Joanna610/Quadrature-amplitude-modulator/antennas_graphs/directional_pattern.jpg

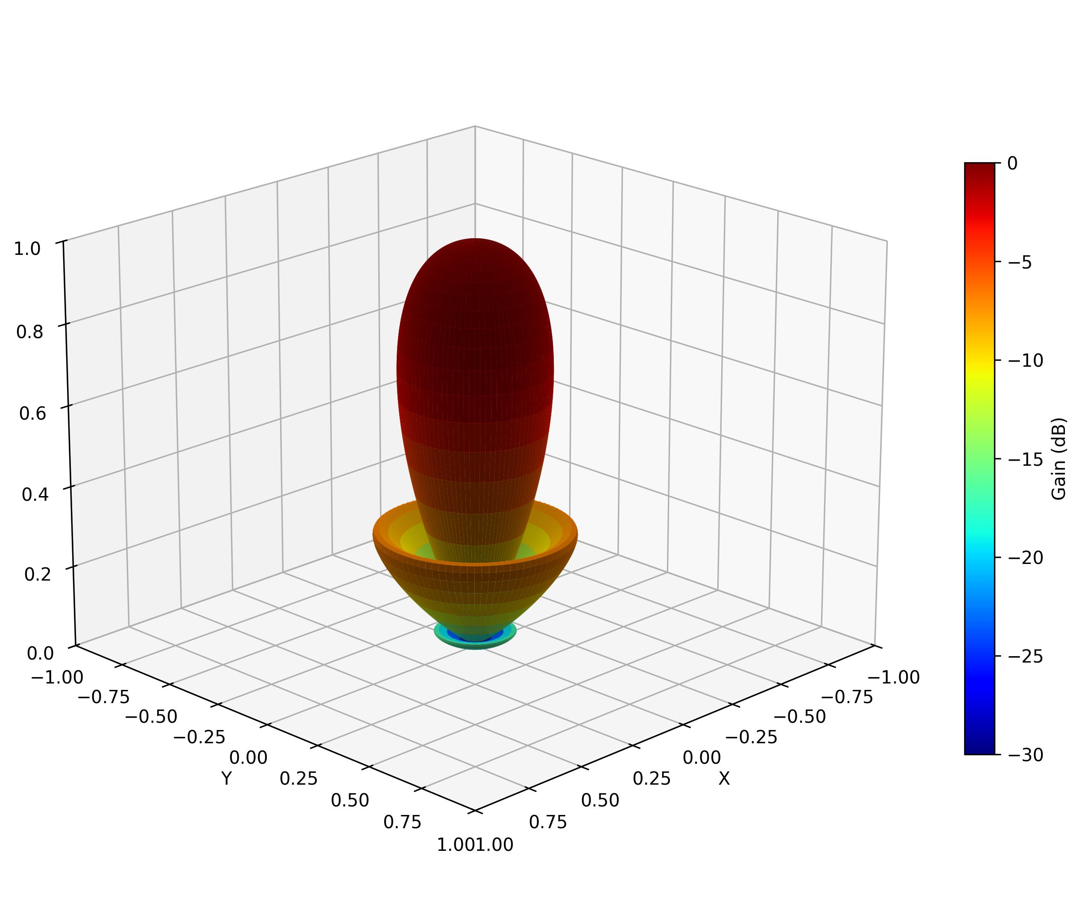
antennas_graphs/directional_pattern.jpg
