Joanna610/Quadrature-amplitude-modulator/antennas_graphs/omi_radiation pattern.jpg

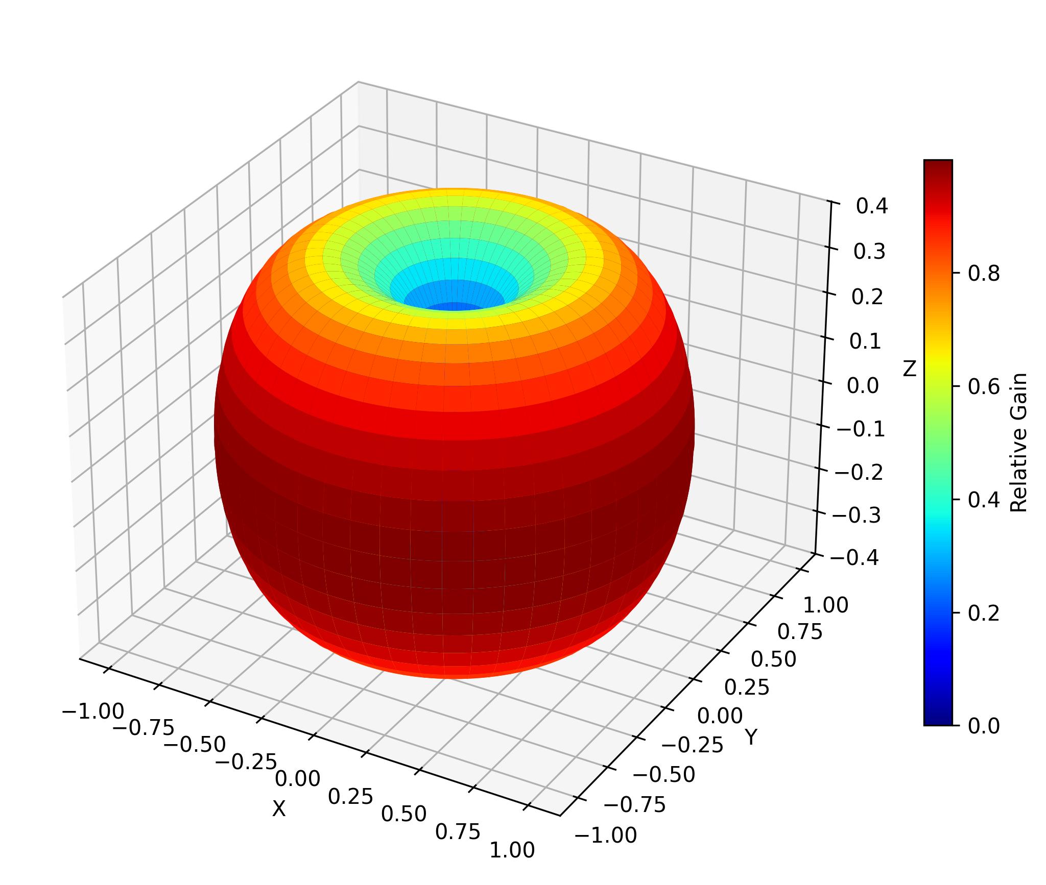
antennas_graphs/omi_radiation pattern.jpg
