Joanna610/Quadrature-amplitude-modulator/antennas_graphs/omi_vertycal.jpg

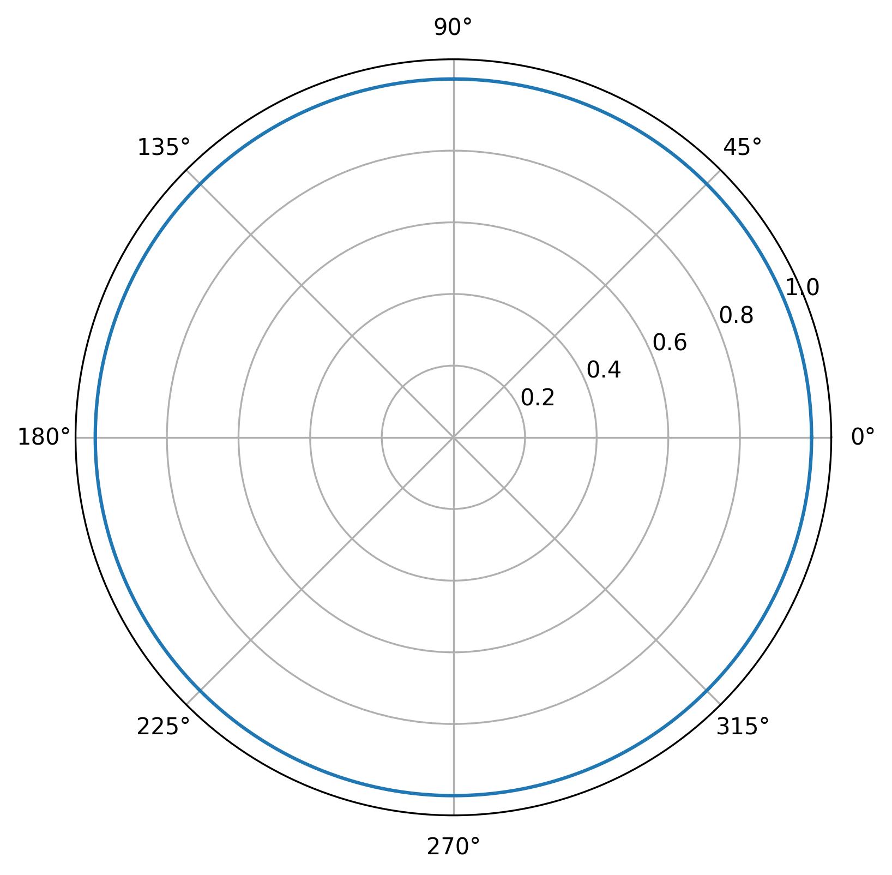
antennas_graphs/omi_vertycal.jpg
