Joanna610/Quadrature-amplitude-modulator/antennas_graphs/omni_2d.jpg

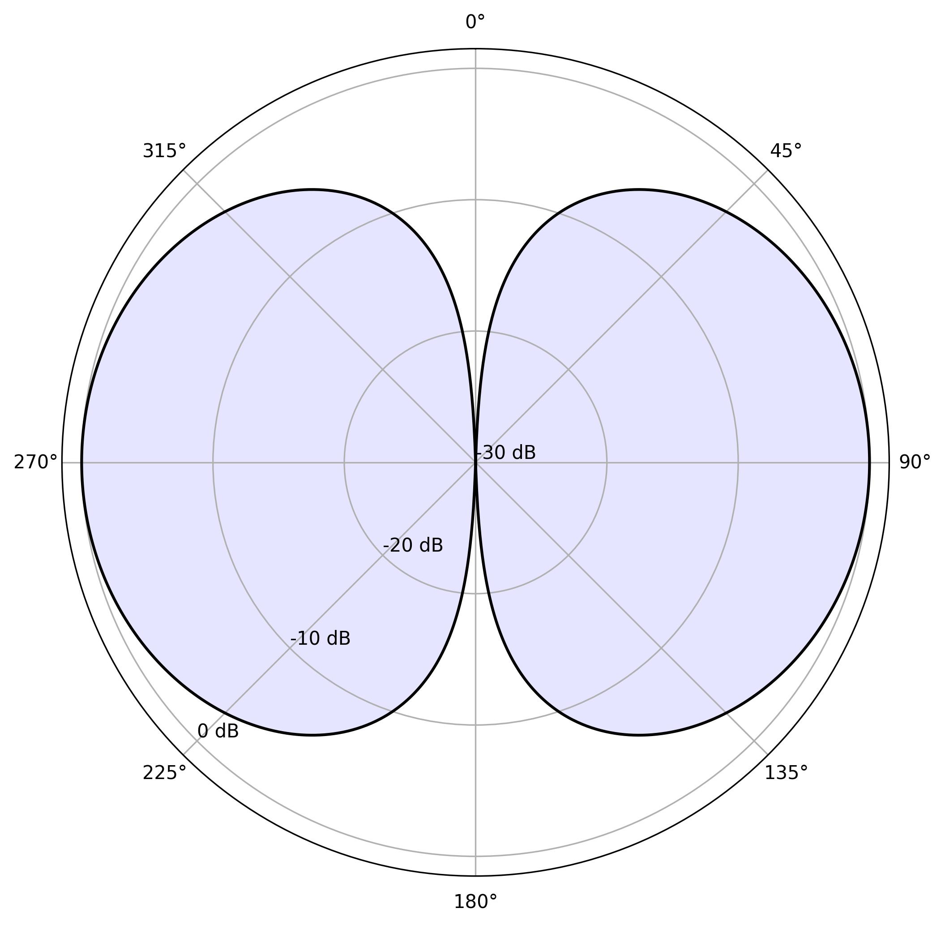
antennas_graphs/omni_2d.jpg
