Joanna610/Quadrature-amplitude-modulator/antennas_graphs/omni_3d.jpg

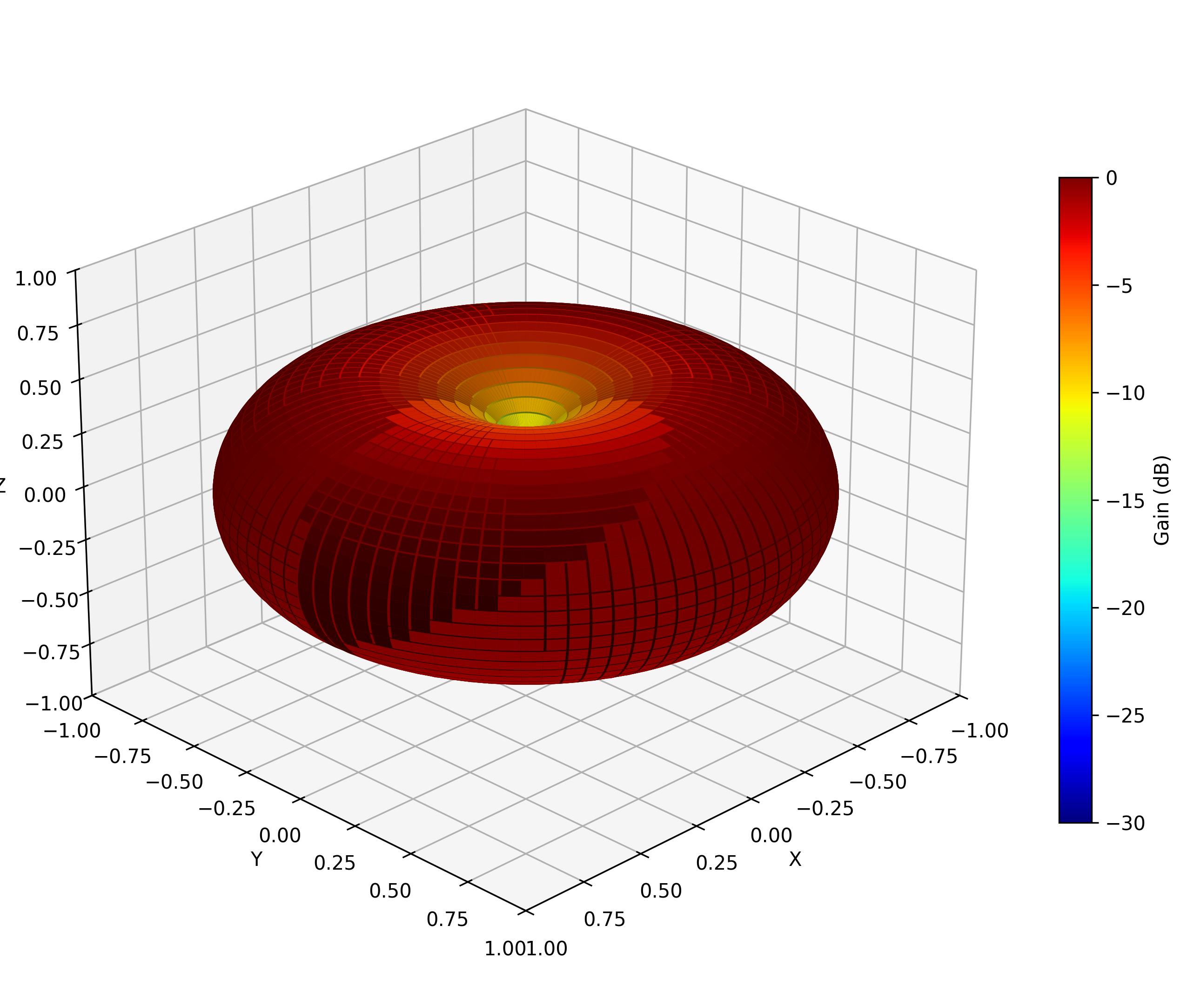
antennas_graphs/omni_3d.jpg
