Joanna610/Quadrature-amplitude-modulator/modulation_graph/4_QAM.jpg

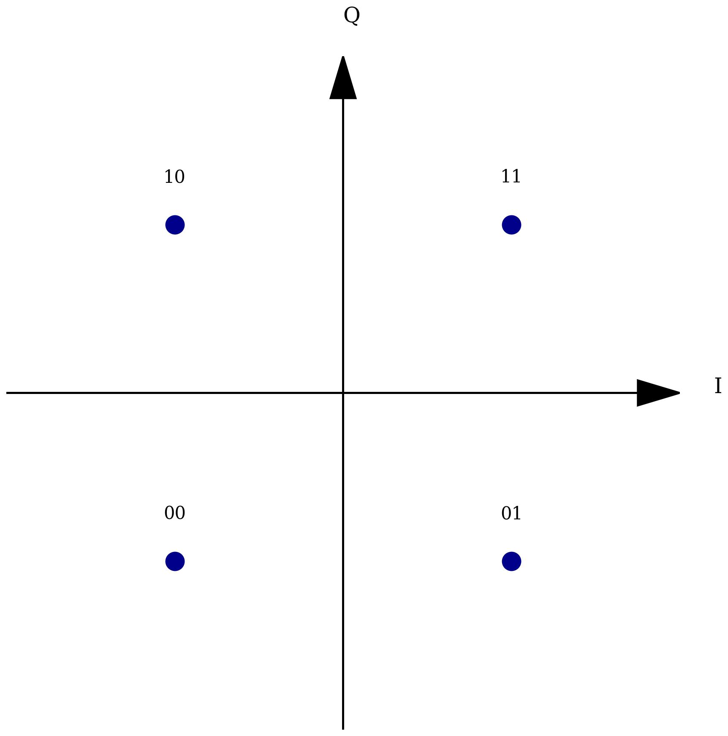
modulation_graph/4_QAM.jpg
