Joanna610/Quadrature-amplitude-modulator/modulation_graph/8PSK.jpg

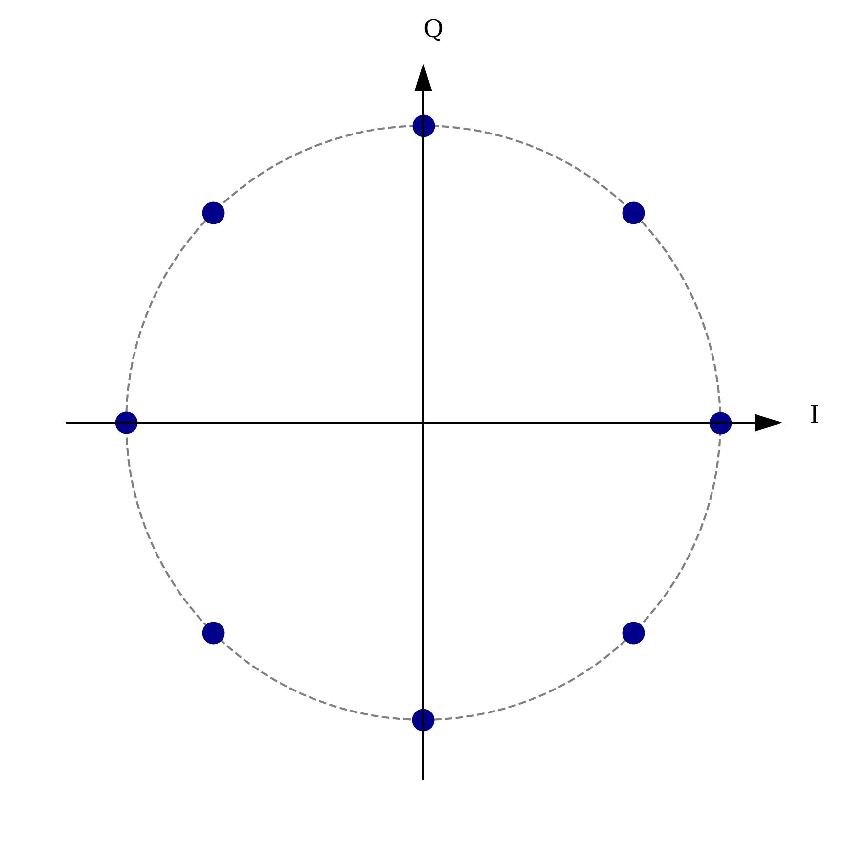
modulation_graph/8PSK.jpg
