Joanna610/Quadrature-amplitude-modulator/modulation_graph/16_QAM.jpg

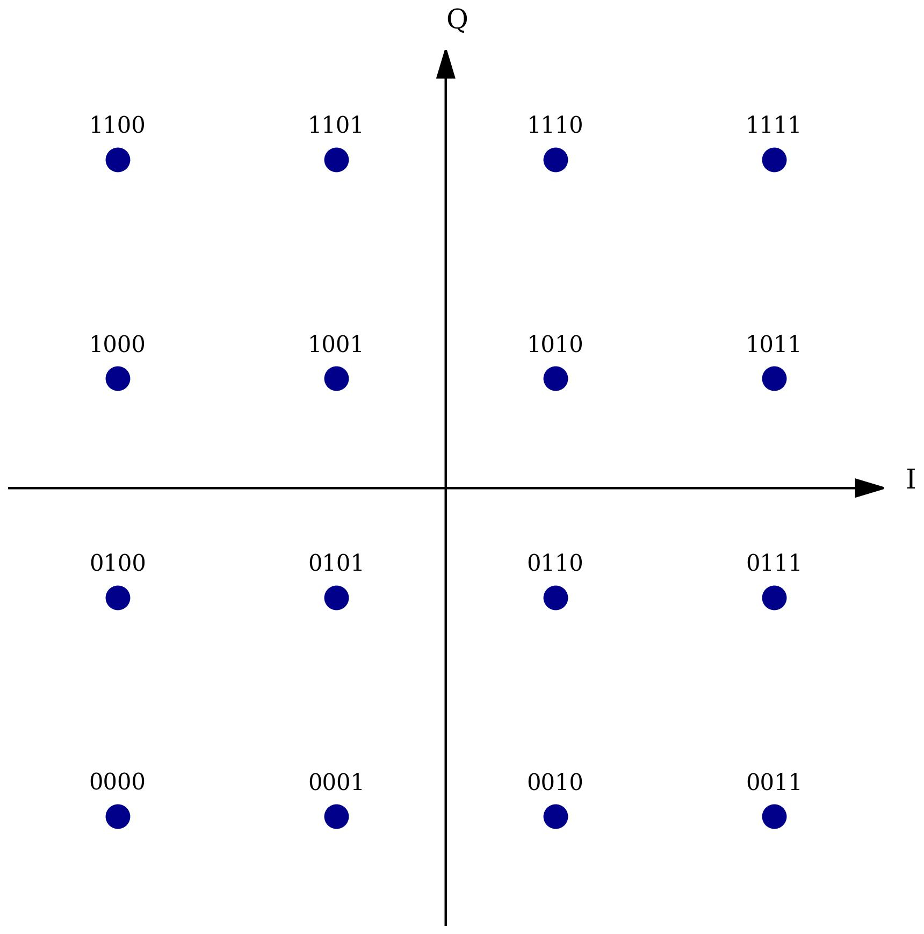
modulation_graph/16_QAM.jpg
