Joanna610/Quadrature-amplitude-modulator/modulation_graph/amplitude_carrier.png

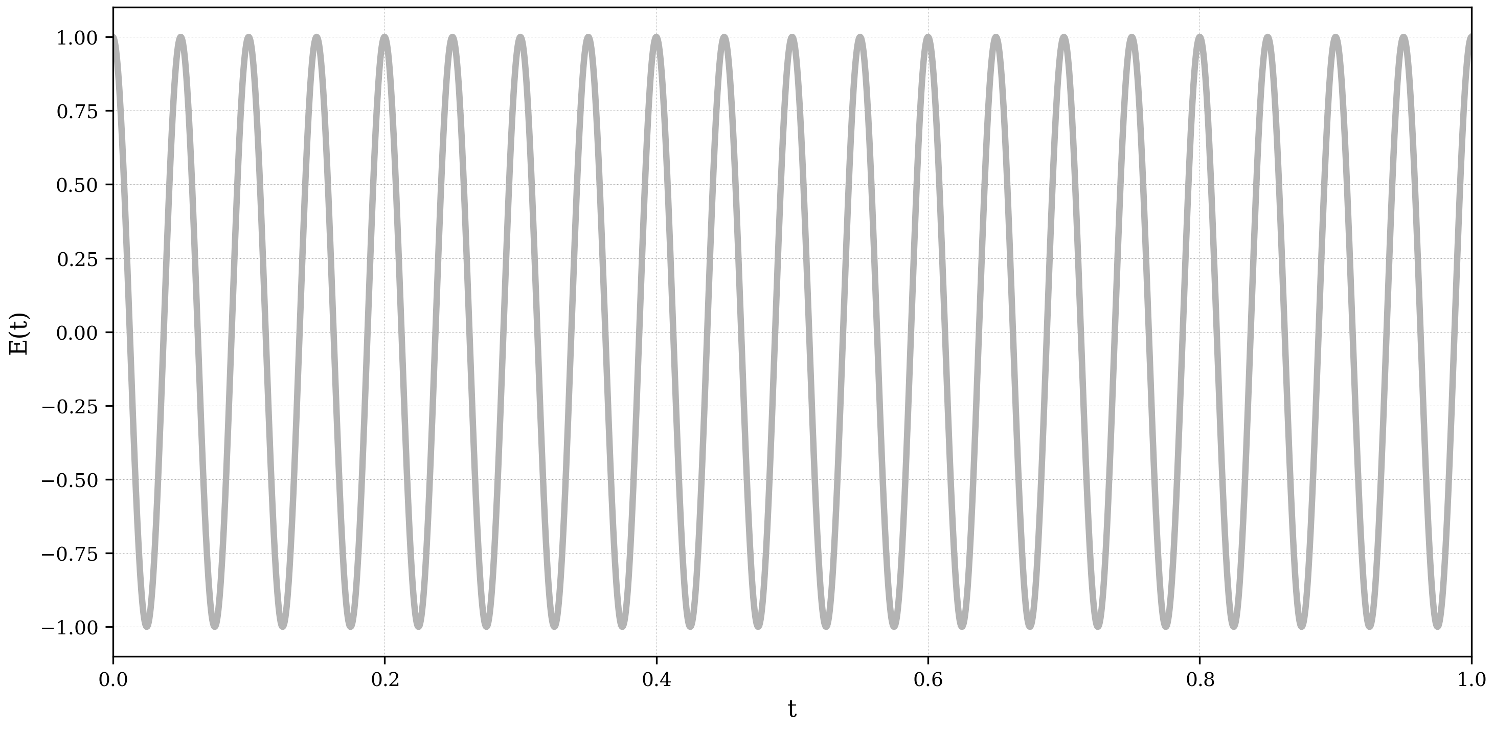
modulation_graph/amplitude_carrier.png
