Joanna610/Quadrature-amplitude-modulator/modulation_graph/amplitude_modulation.jpg

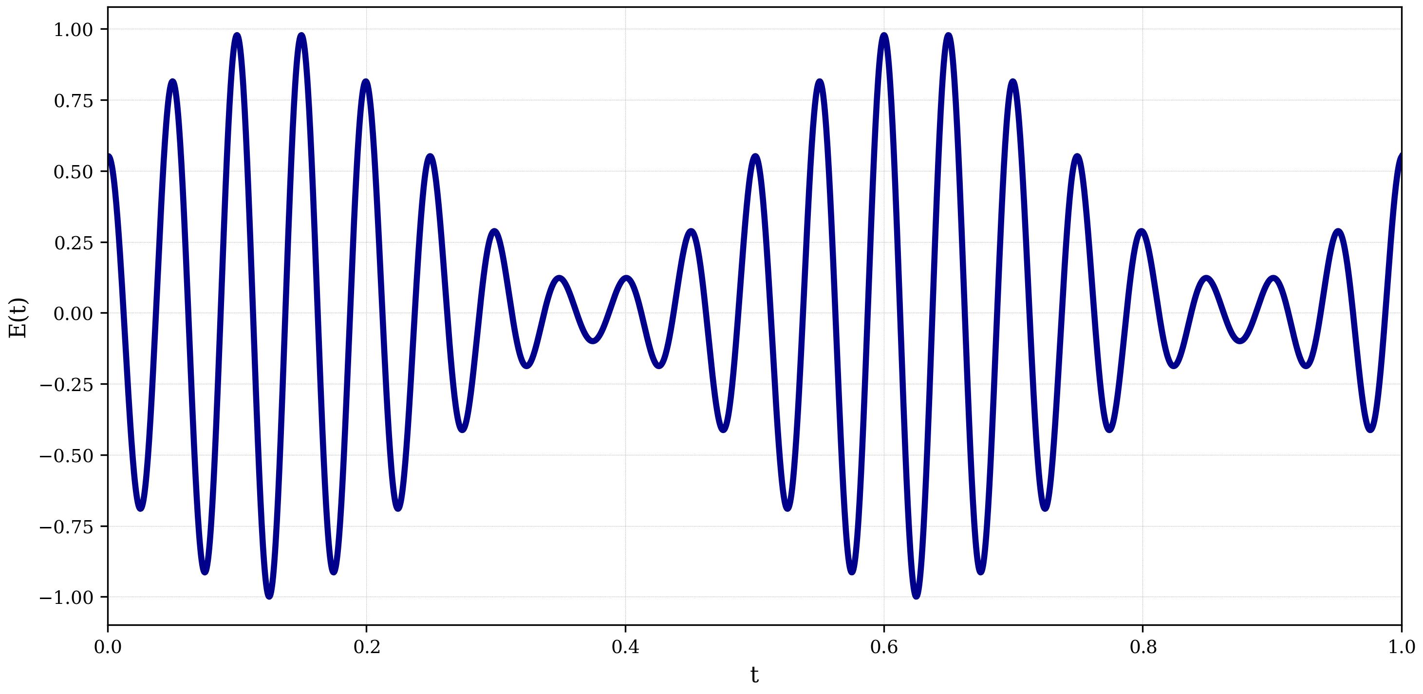
modulation_graph/amplitude_modulation.jpg
