Joanna610/Quadrature-amplitude-modulator/modulation_graph/amplitude_signal.png

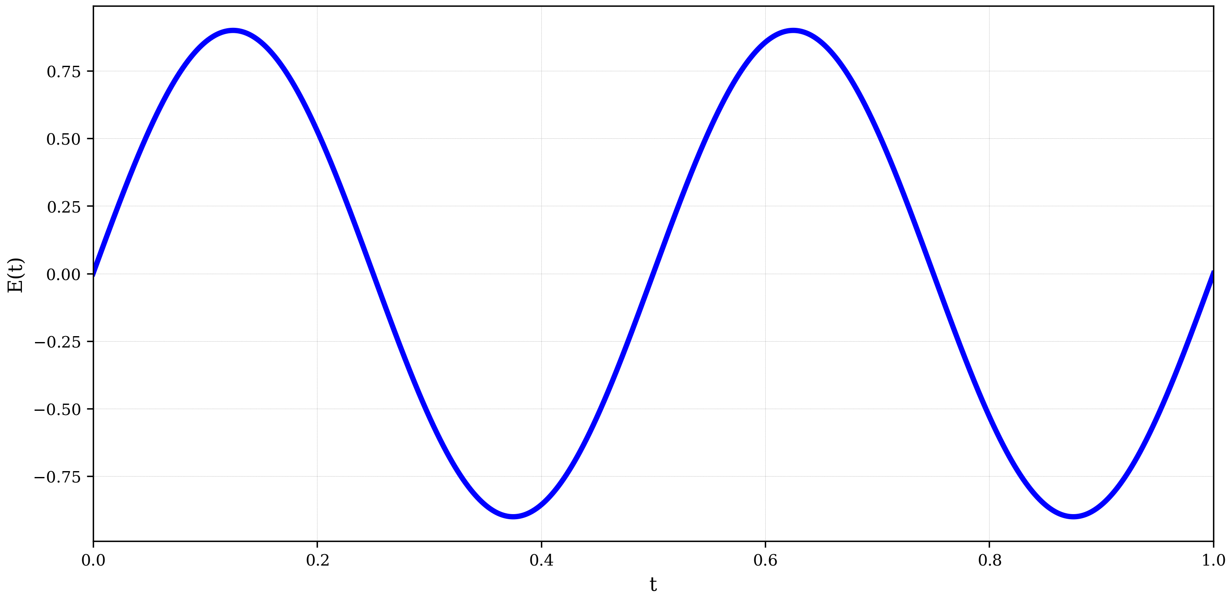
modulation_graph/amplitude_signal.png
