Joanna610/Quadrature-amplitude-modulator/modulation_graph/ASK.jpg

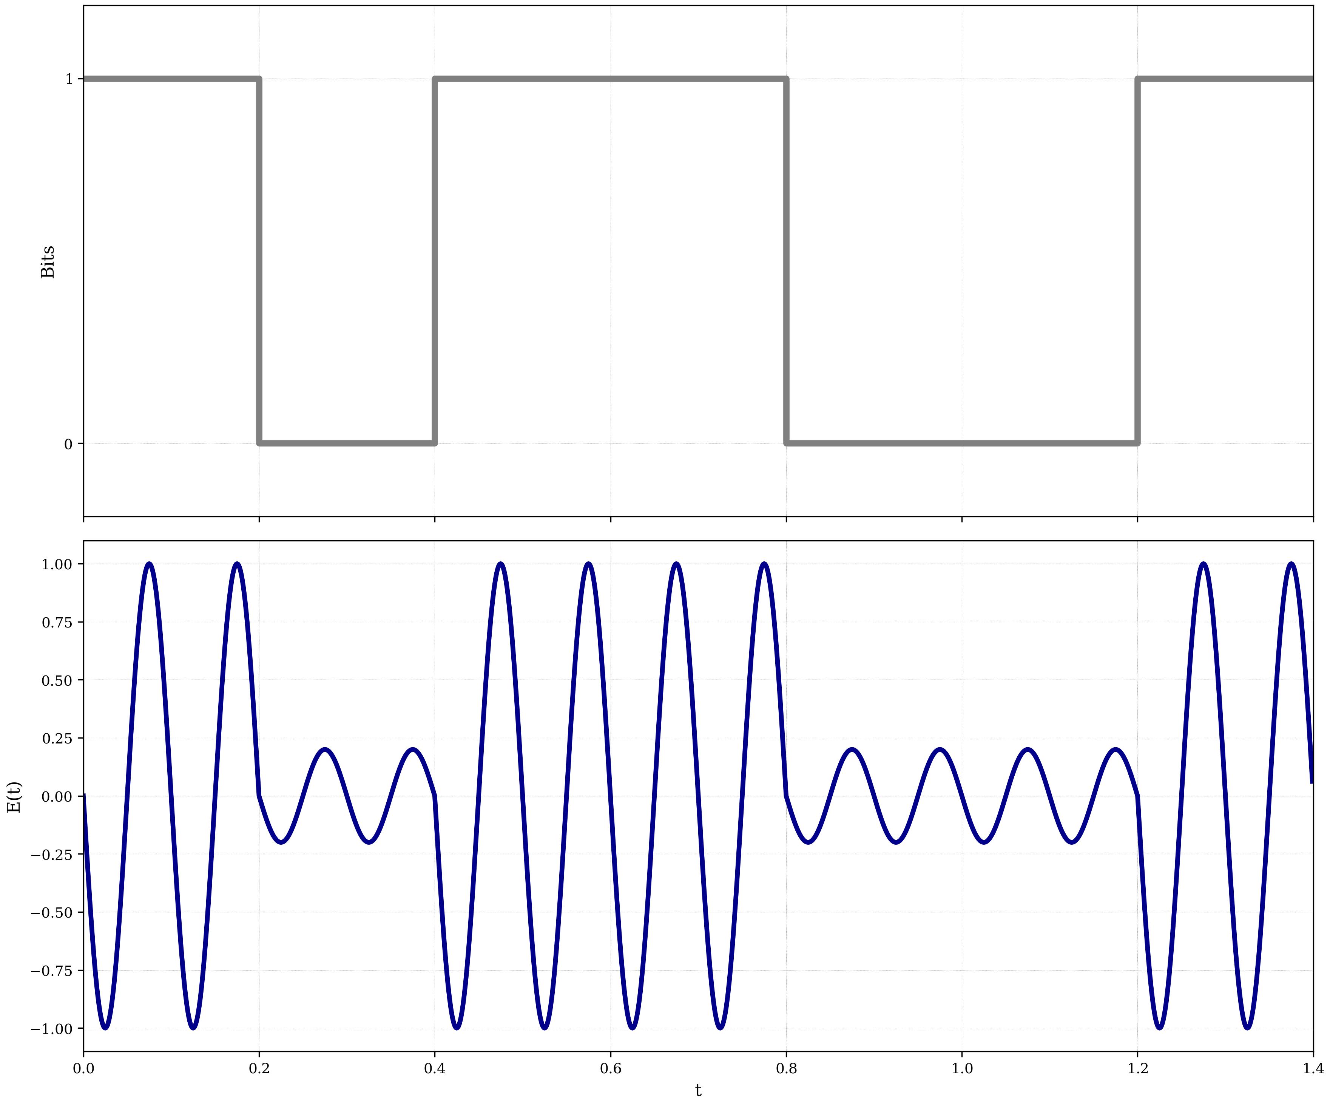
modulation_graph/ASK.jpg
