Joanna610/Quadrature-amplitude-modulator/modulation_graph/bpsk.jpg

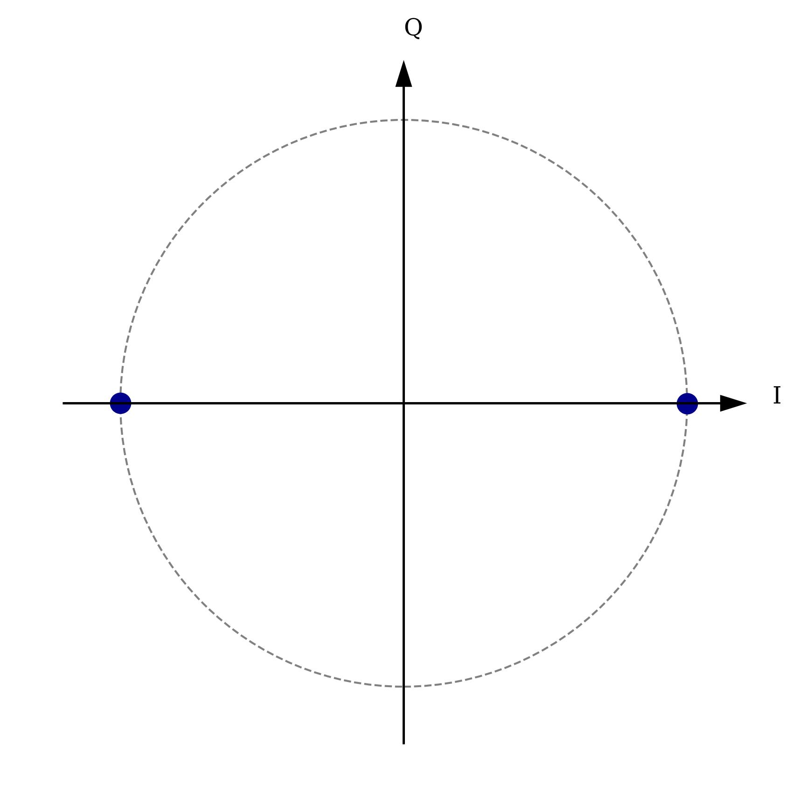
modulation_graph/bpsk.jpg
