Joanna610/Quadrature-amplitude-modulator/modulation_graph/frequency_modulation.jpg

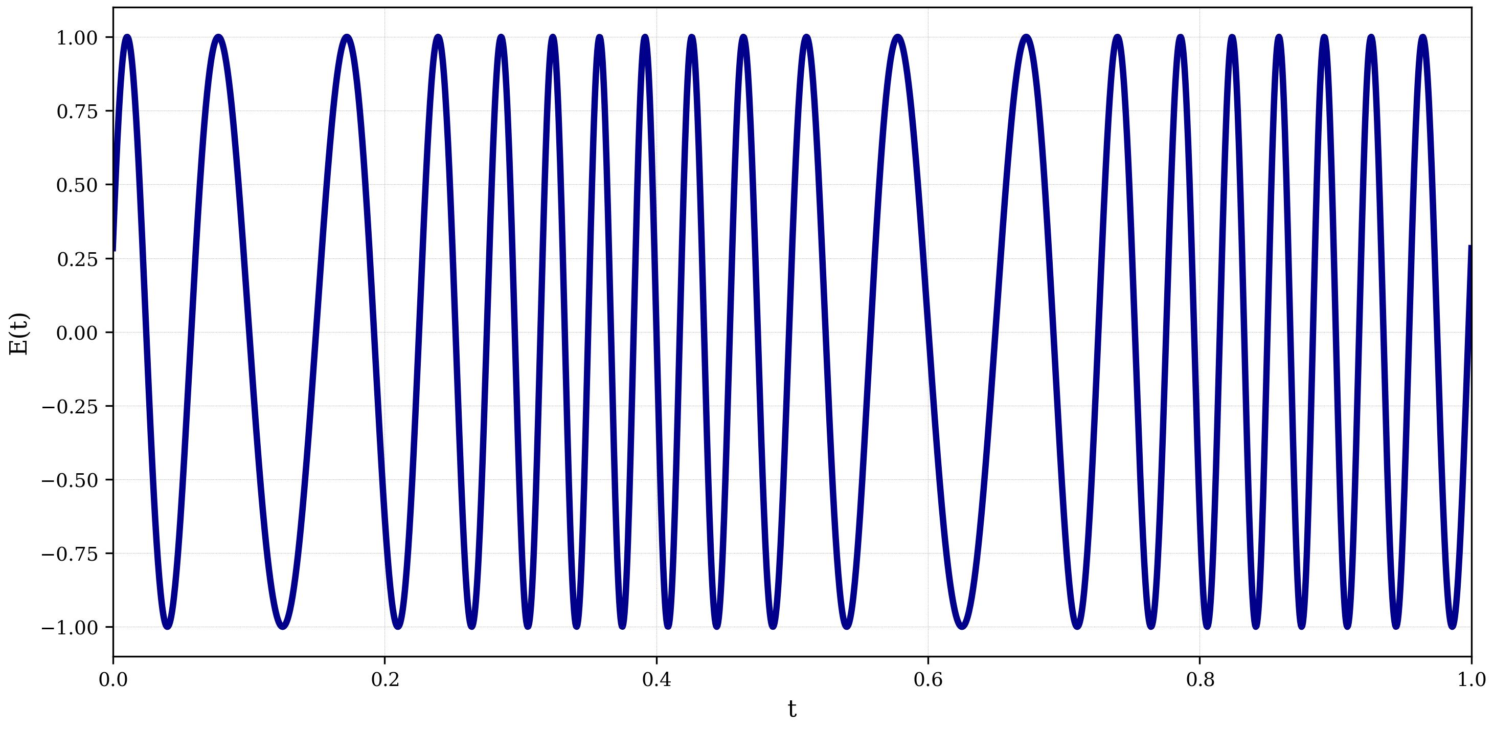
modulation_graph/frequency_modulation.jpg
