Joanna610/Quadrature-amplitude-modulator/modulation_graph/frequency_signal.png

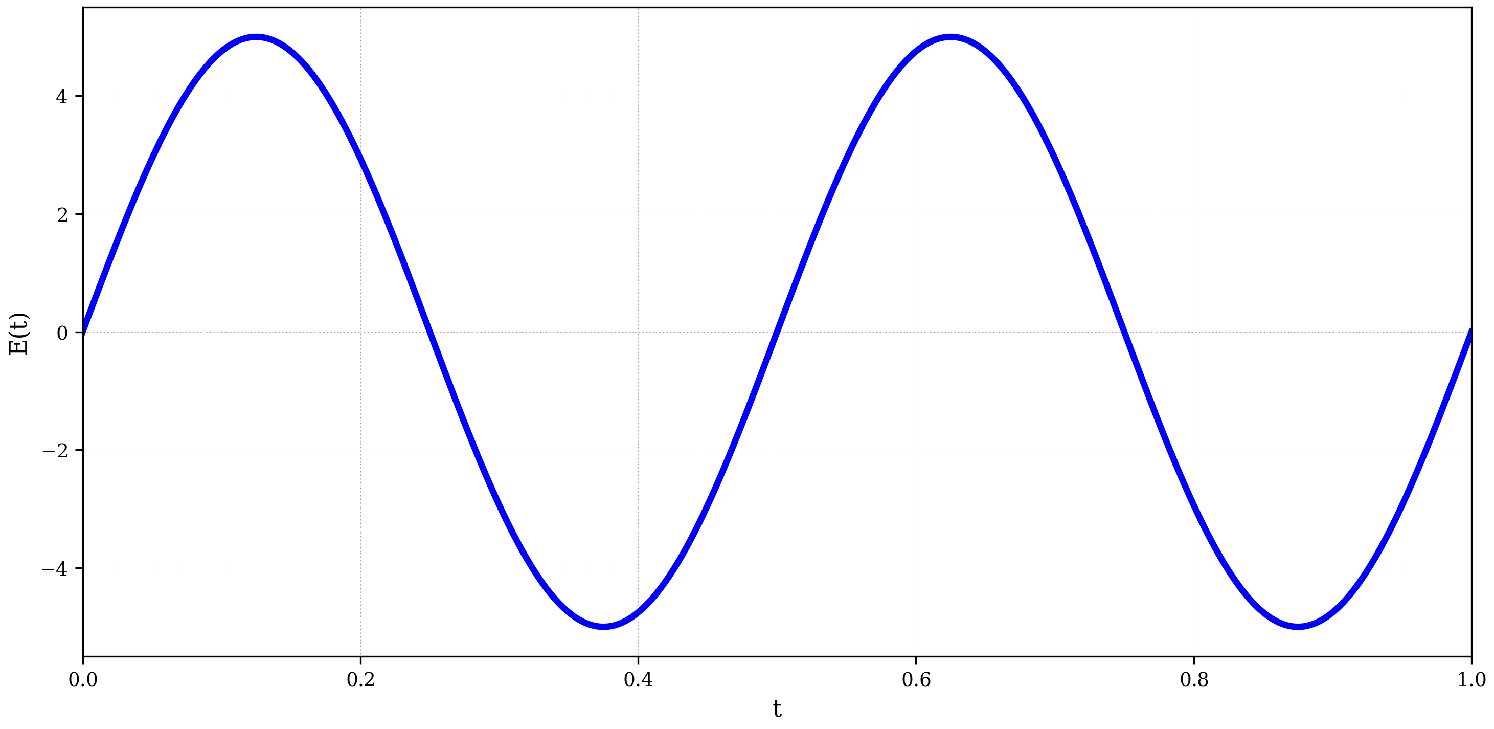
modulation_graph/frequency_signal.png
