Joanna610/Quadrature-amplitude-modulator/modulation_graph/FSK.jpg

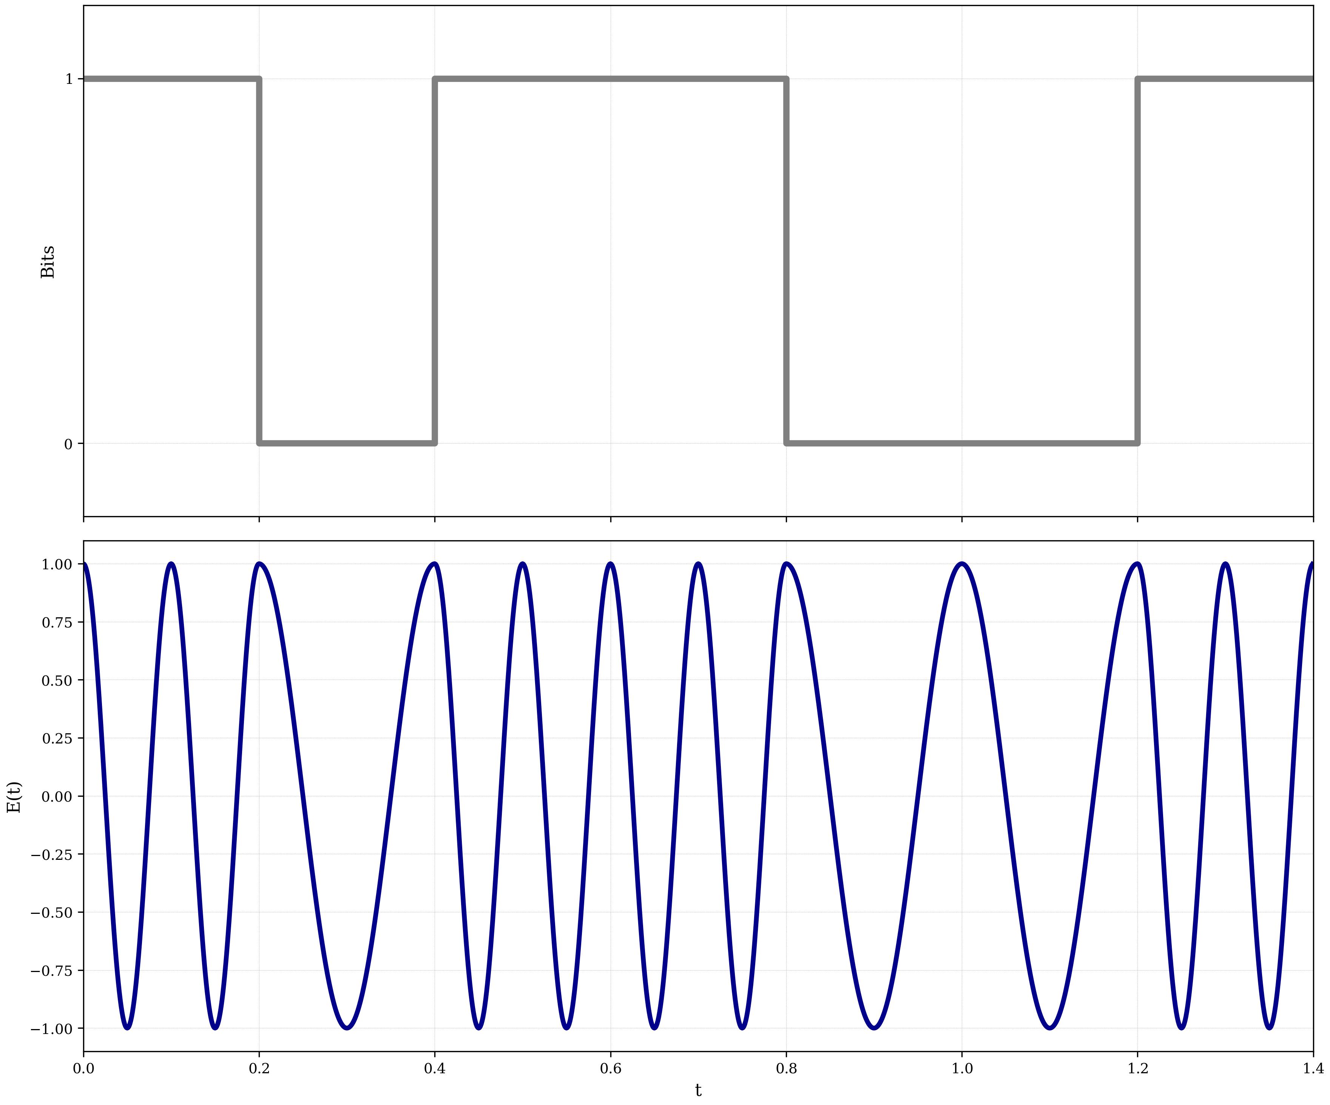
modulation_graph/FSK.jpg
