Joanna610/Quadrature-amplitude-modulator/modulation_graph/phase_modulation.jpg

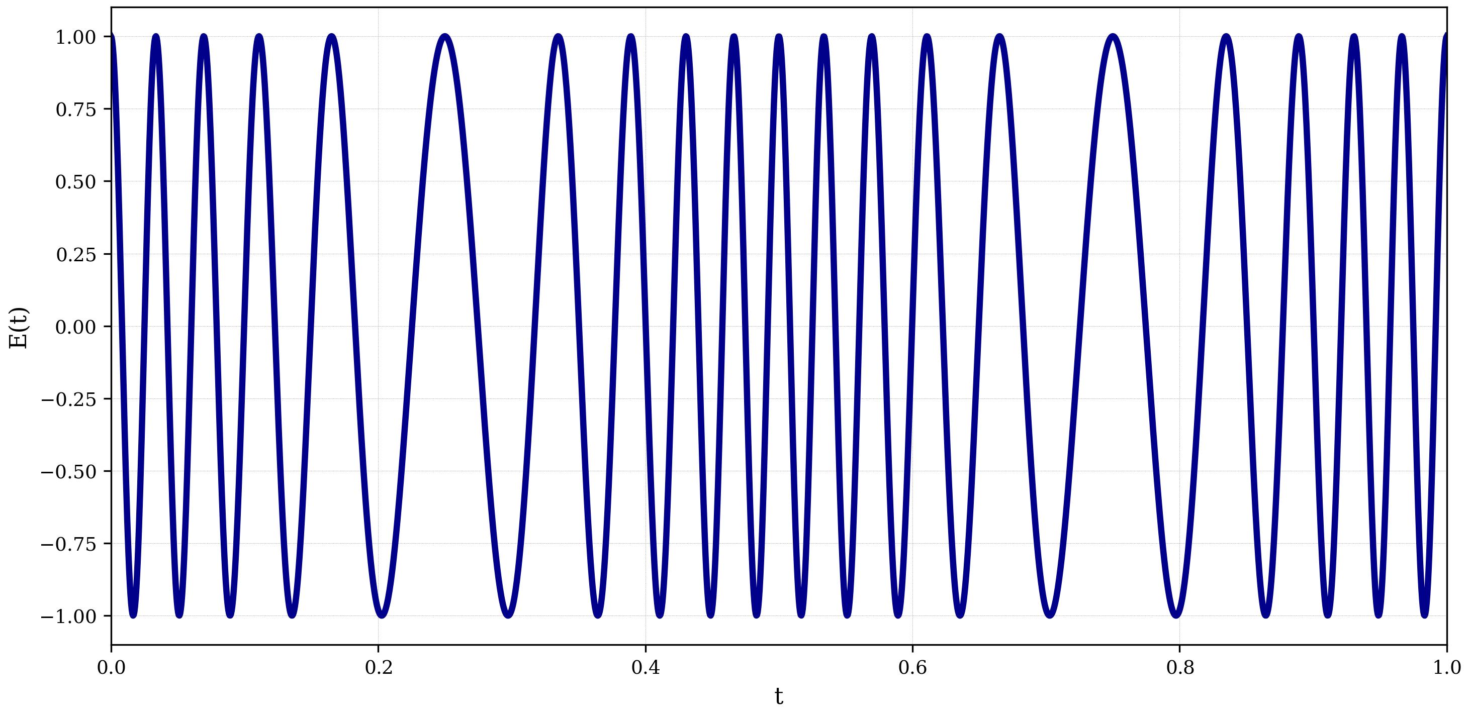
modulation_graph/phase_modulation.jpg
