Joanna610/Quadrature-amplitude-modulator/modulation_graph/PSK.jpg

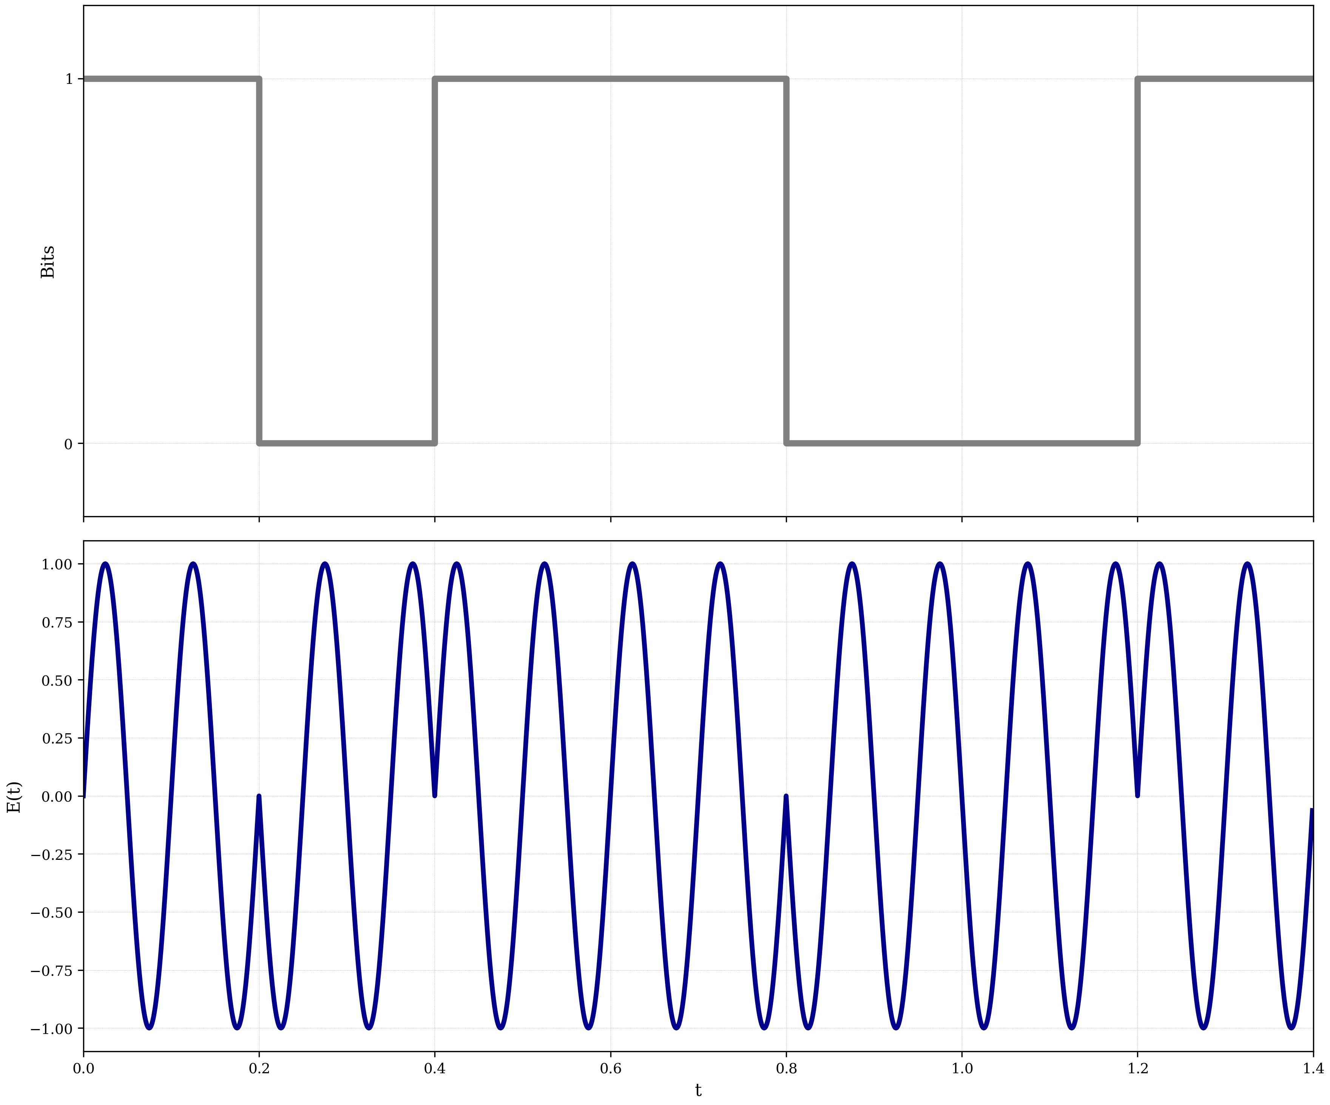
modulation_graph/PSK.jpg
