Joanna610/Quadrature-amplitude-modulator/transmiter/max2608.png

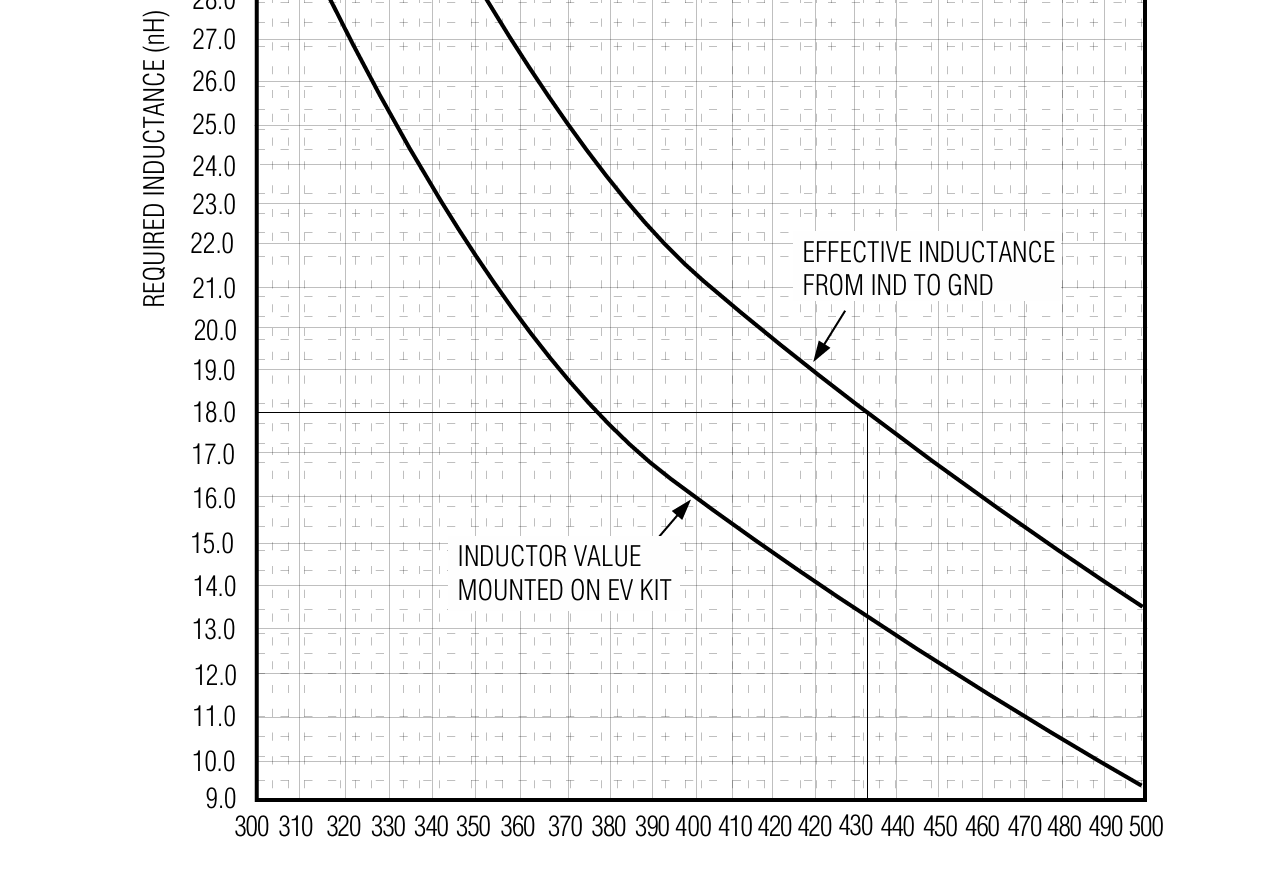
transmiter/max2608.png
