Joanna610/Quadrature-amplitude-modulator/wave.png

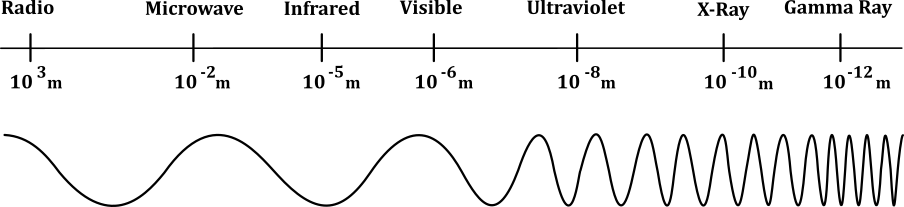
wave.png
