Joanna610/Quadrature-amplitude-modulator/antennas_graphs/test.jpg

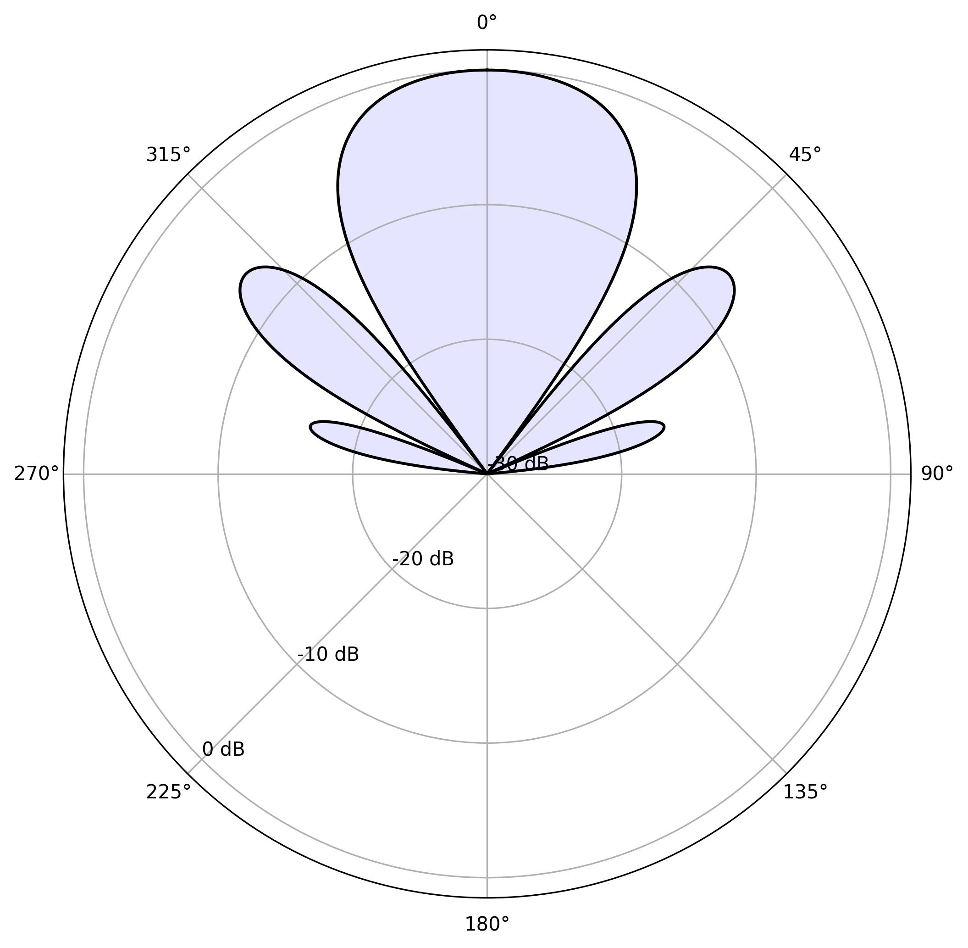
antennas_graphs/test.jpg
