Joanna610/Quadrature-amplitude-modulator/receiver/measurements/all_system_different_frequencies/gen_413_output_-16dBm.png

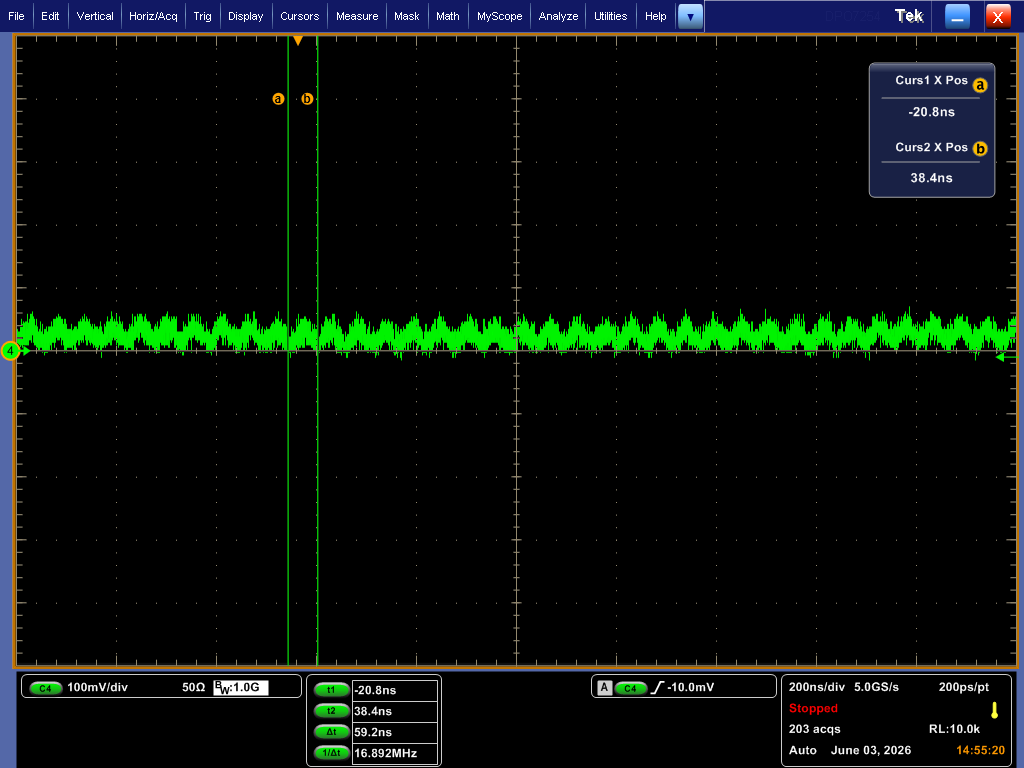
receiver/measurements/all_system_different_frequencies/gen_413_output_-16dBm.png
