Joanna610/Quadrature-amplitude-modulator/receiver/measurements/all_system_together_433MHz/433MHz_-13dBm_RF_from_transformator.png

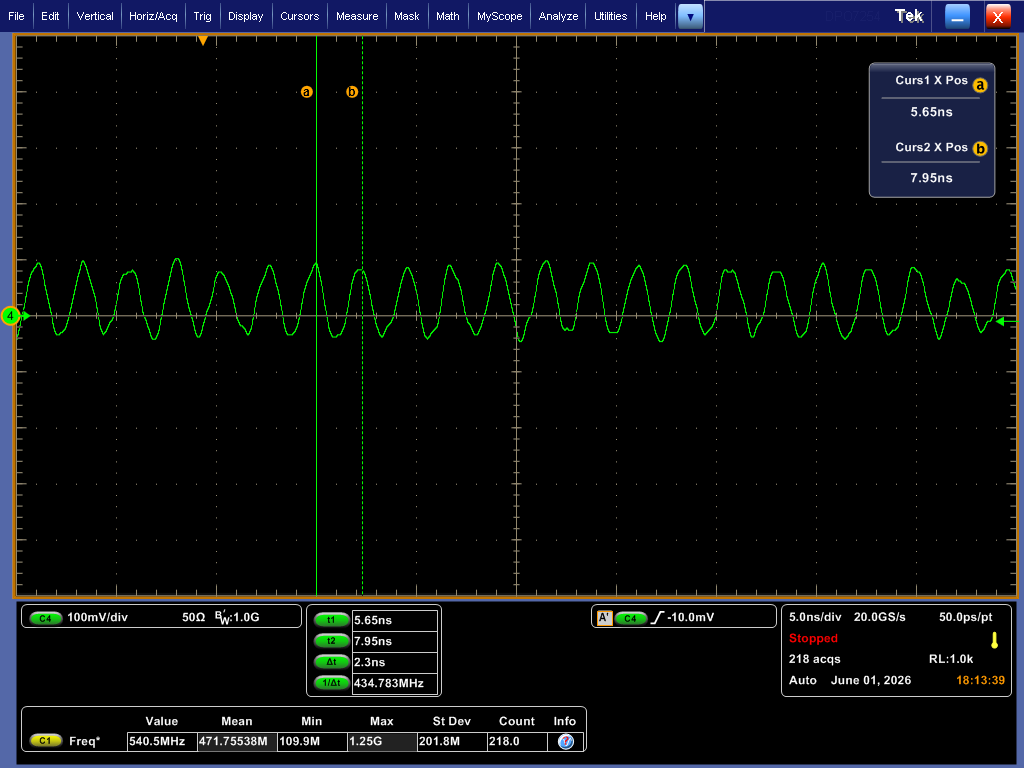
receiver/measurements/all_system_together_433MHz/433MHz_-13dBm_RF_from_transformator.png
