Joanna610/Quadrature-amplitude-modulator/receiver/measurements/all_system_together_433MHz/433MHz_-16dBm_pączek_I_differential_Q_single_ended.png

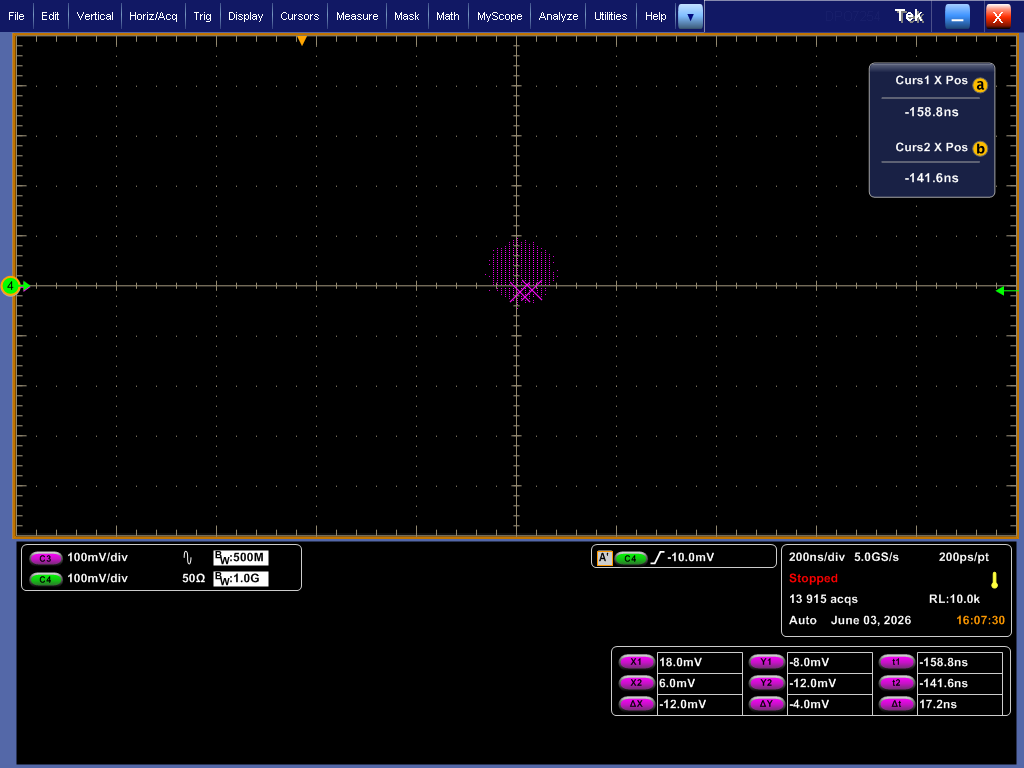
receiver/measurements/all_system_together_433MHz/433MHz_-16dBm_pączek_I_differential_Q_single_ended.png
