Joanna610/Quadrature-amplitude-modulator/receiver/measurements/all_system_together_433MHz/LO_jpg/433MHz_-16dBm_LO.jpg

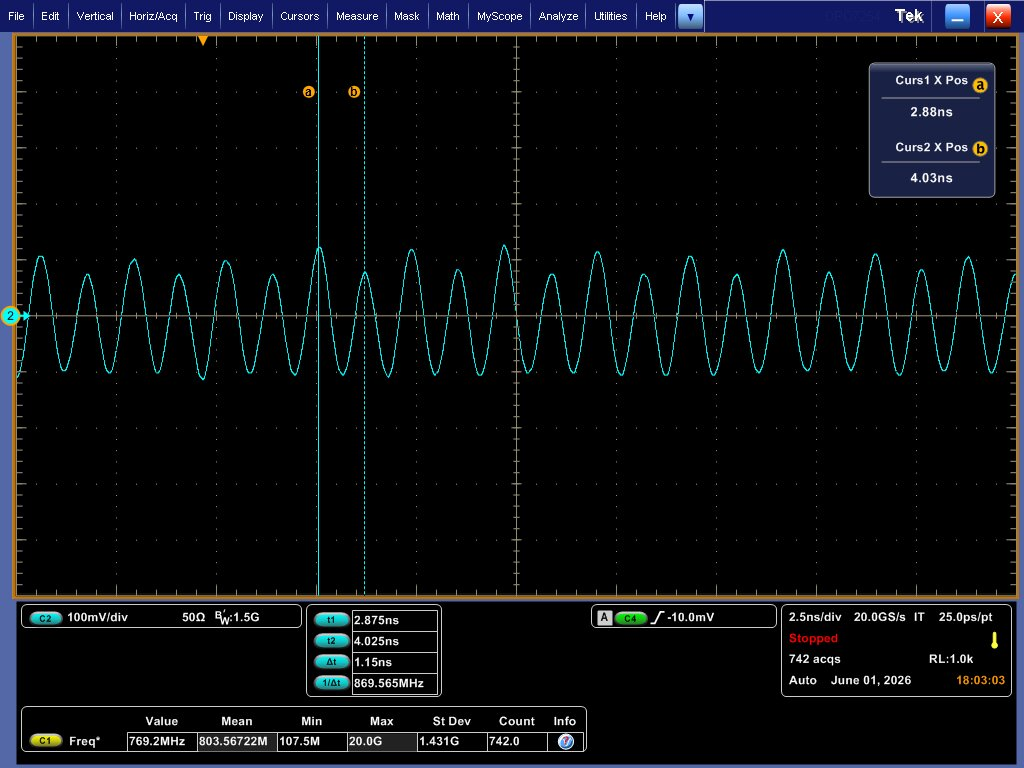
receiver/measurements/all_system_together_433MHz/LO_jpg/433MHz_-16dBm_LO.jpg
