Joanna610/Quadrature-amplitude-modulator/receiver/measurements/all_system_together_433MHz/OUTPUT_jpg/433MHz_-13dBm_output_from_demodulator.jpg

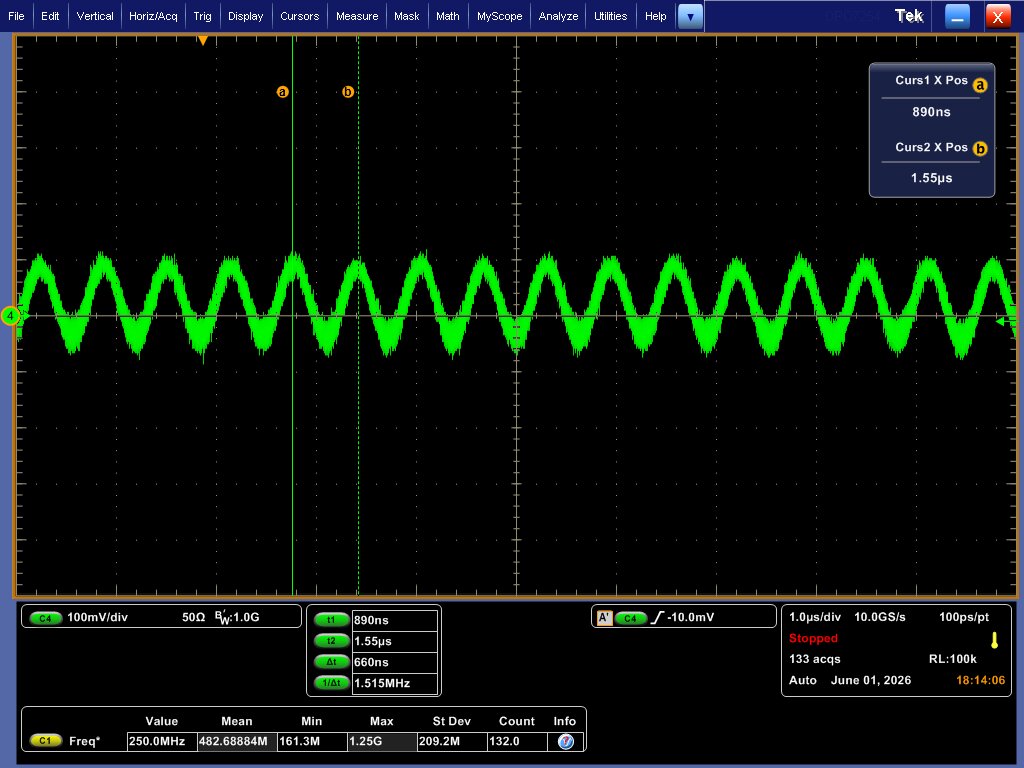
receiver/measurements/all_system_together_433MHz/OUTPUT_jpg/433MHz_-13dBm_output_from_demodulator.jpg
