Joanna610/Quadrature-amplitude-modulator/receiver/measurements/all_system_together_433MHz/OUTPUT_jpg/433Mhz_-17dBm_output_demodulator.jpg

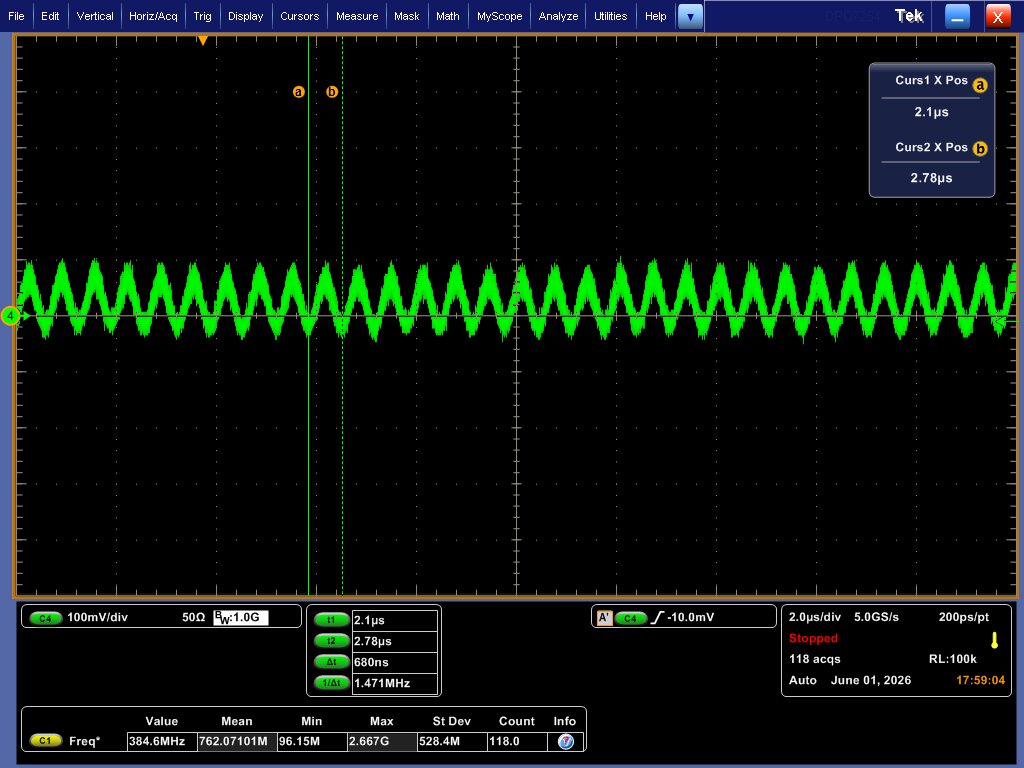
receiver/measurements/all_system_together_433MHz/OUTPUT_jpg/433Mhz_-17dBm_output_demodulator.jpg
