Joanna610/Quadrature-amplitude-modulator/receiver/measurements/all_system_together_433MHz/RF_jpg/433MHz_-12dBm_RF_from_transformator.jpg

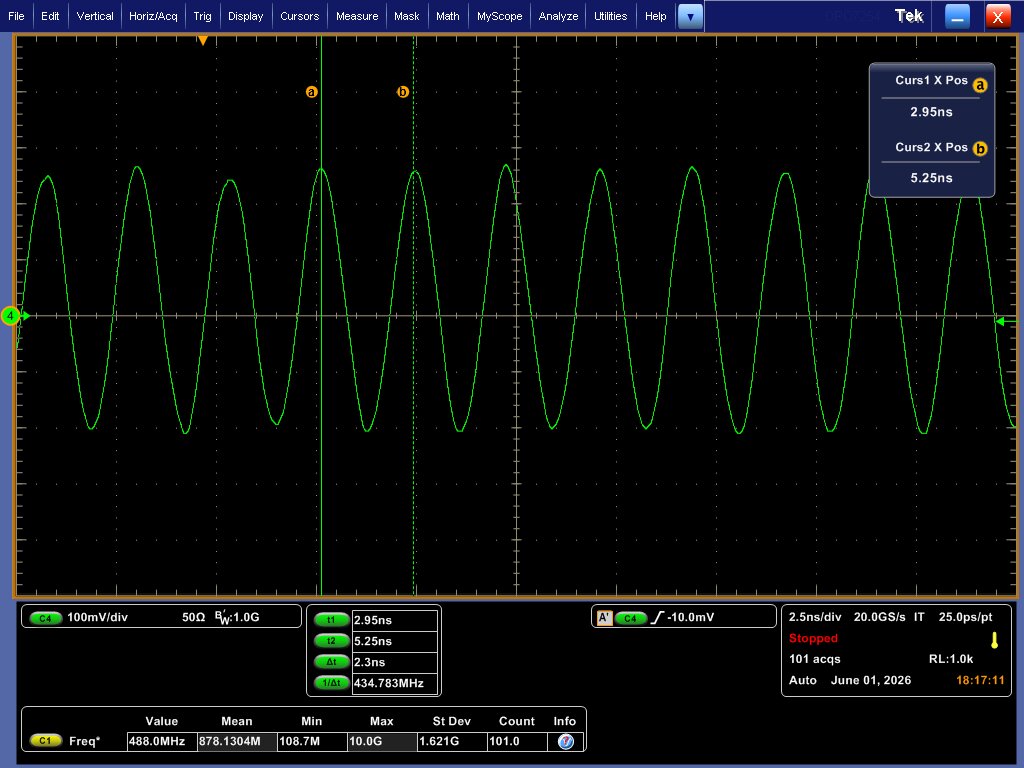
receiver/measurements/all_system_together_433MHz/RF_jpg/433MHz_-12dBm_RF_from_transformator.jpg
