Joanna610/Quadrature-amplitude-modulator/receiver/measurements/band_pass/band_pas__filter_2.png

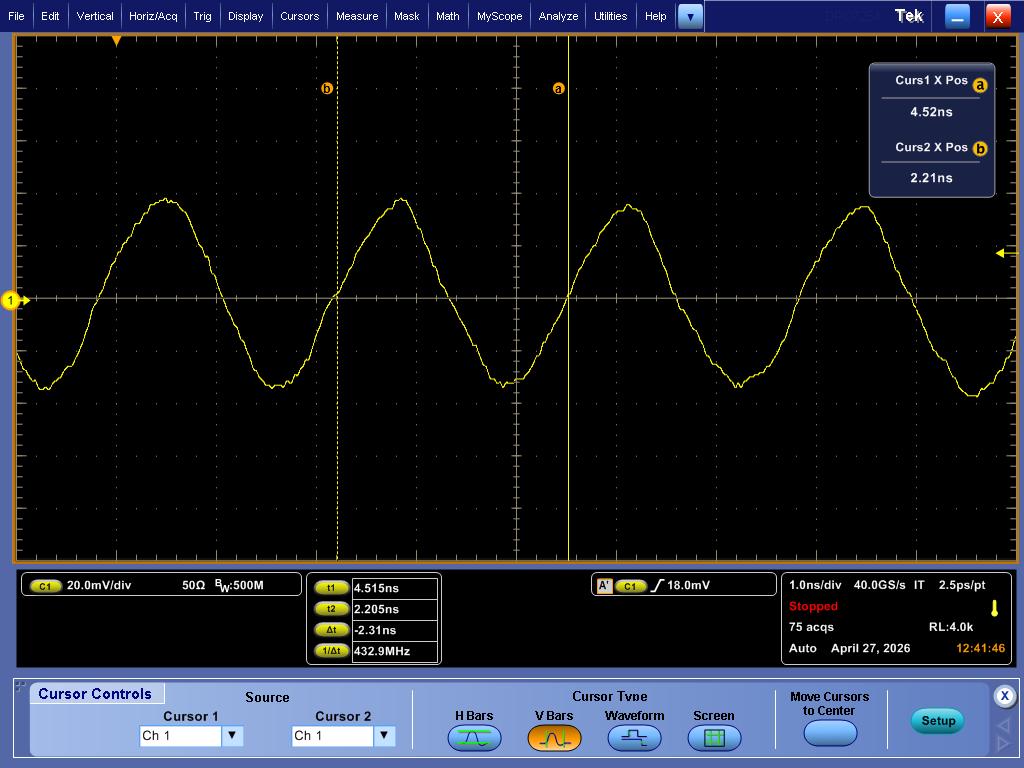
receiver/measurements/band_pass/band_pas__filter_2.png
