Joanna610/Quadrature-amplitude-modulator/receiver/measurements/band_pass/band_pass_C2_kondensator.png

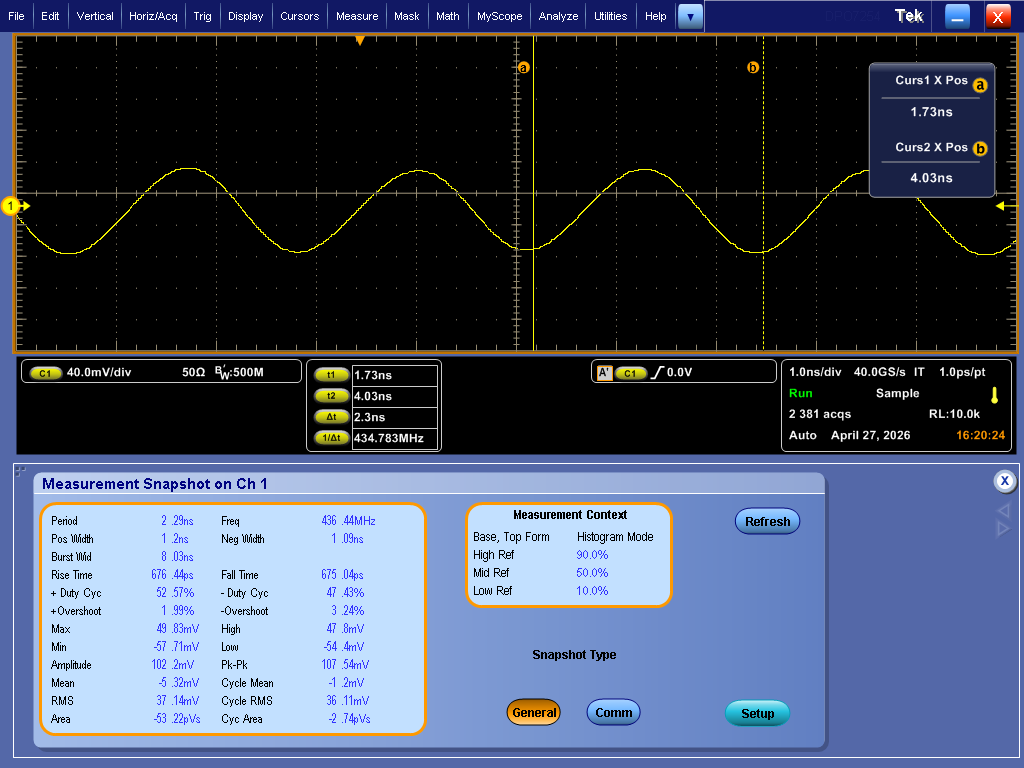
receiver/measurements/band_pass/band_pass_C2_kondensator.png
