Joanna610/Quadrature-amplitude-modulator/receiver/measurements/band_pass/band_pass_filter.png

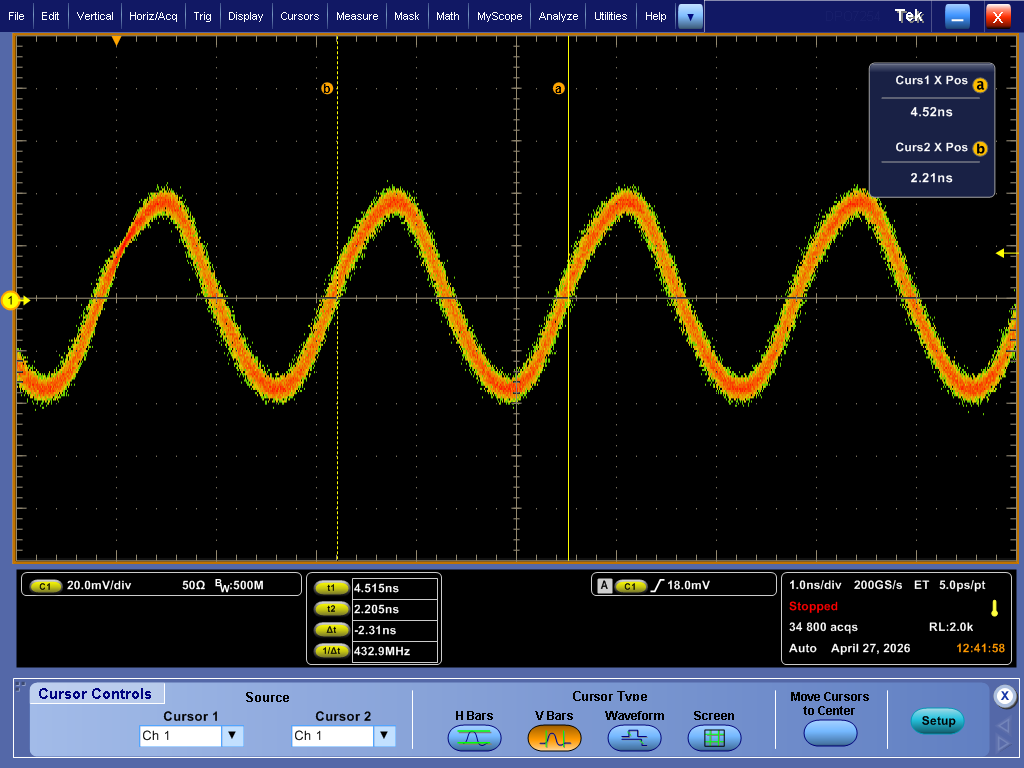
receiver/measurements/band_pass/band_pass_filter.png
