Joanna610/Quadrature-amplitude-modulator/receiver/measurements/band_pass/new_measurement/band_pass_413.png

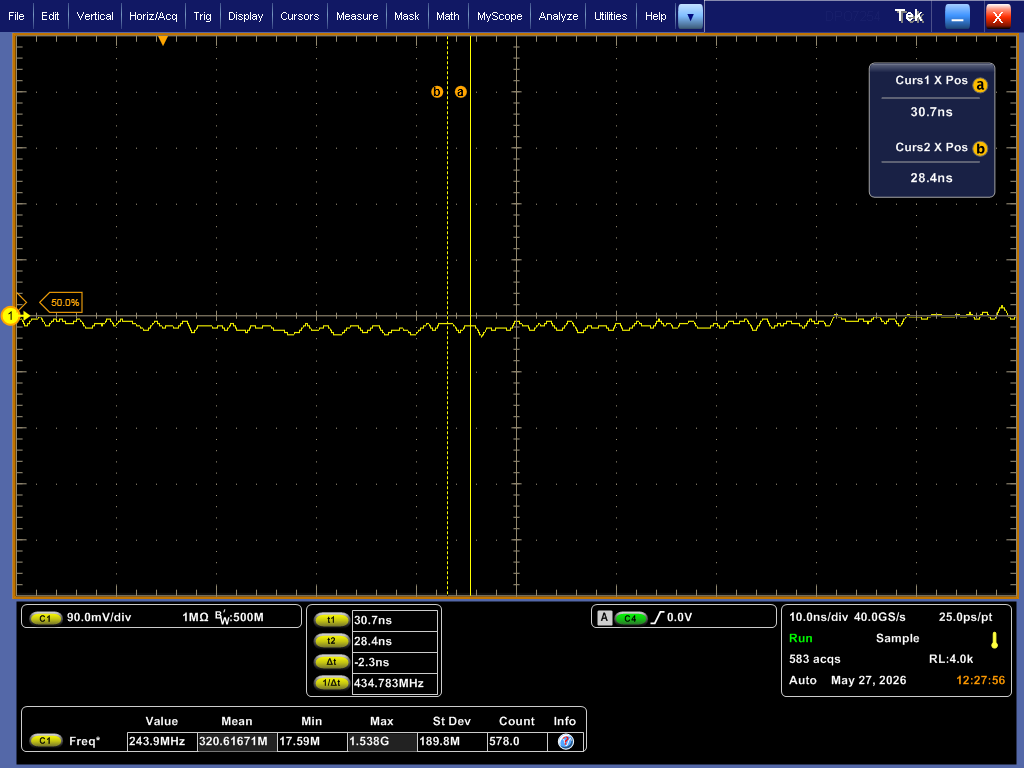
receiver/measurements/band_pass/new_measurement/band_pass_413.png
