Joanna610/Quadrature-amplitude-modulator/receiver/measurements/band_pass/new_measurement/comparizon_band_pass_3.png

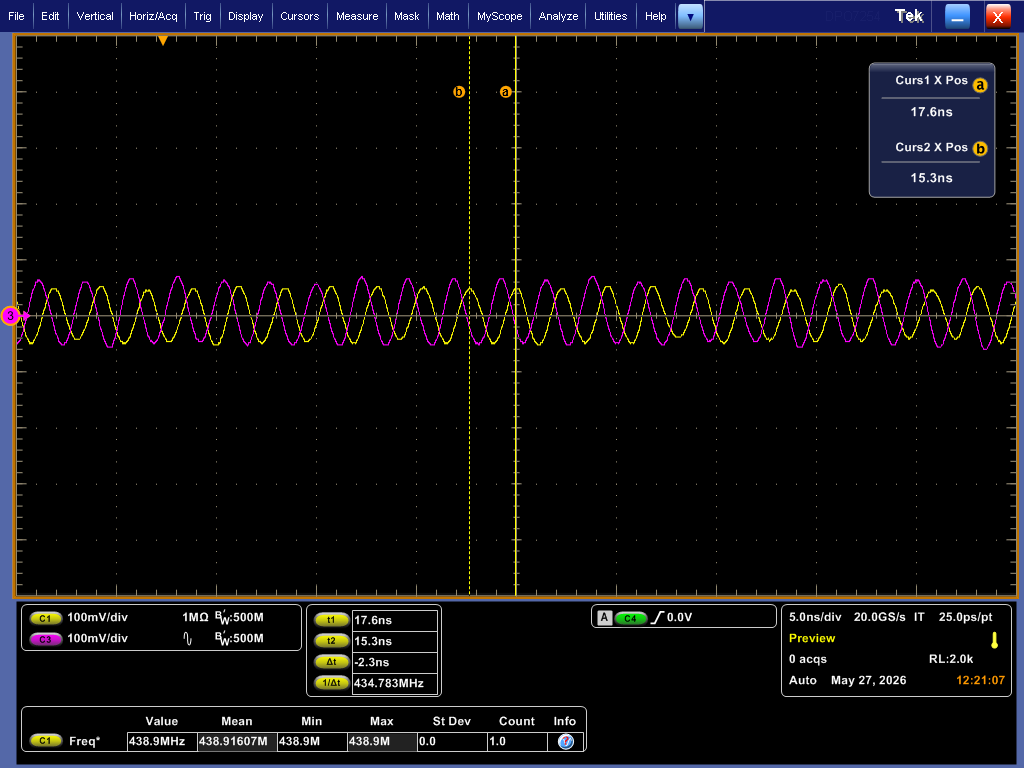
receiver/measurements/band_pass/new_measurement/comparizon_band_pass_3.png
