Joanna610/Quadrature-amplitude-modulator/receiver/measurements/device-out-100mhz-lowpower018.png

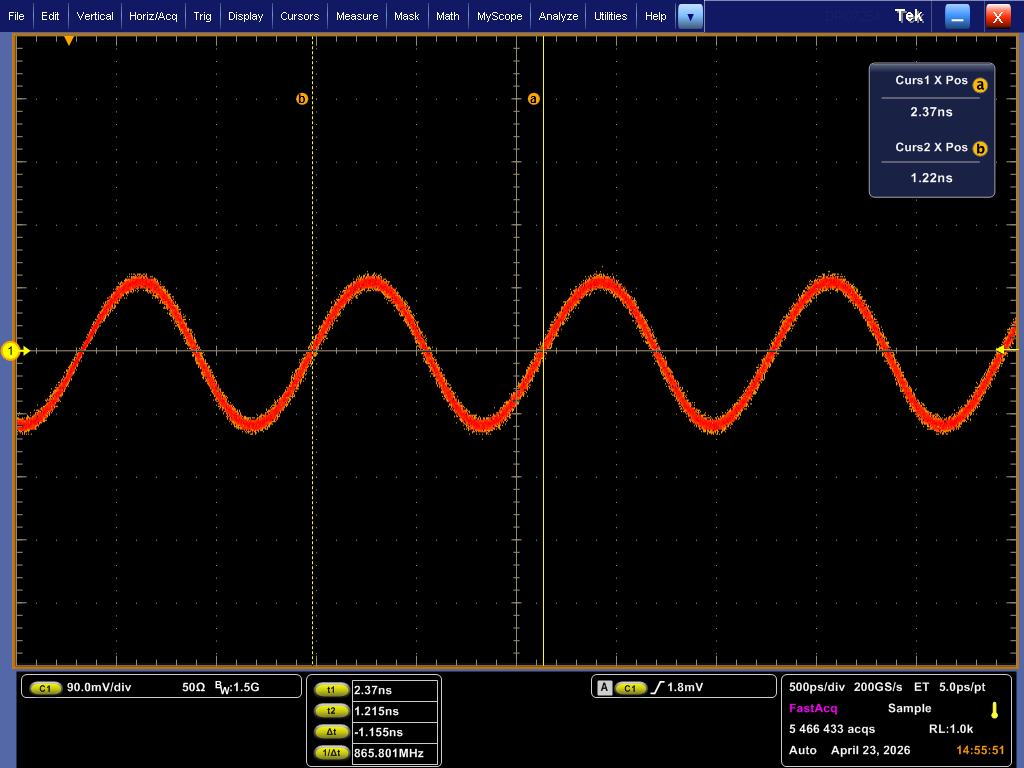
receiver/measurements/device-out-100mhz-lowpower018.png
