Joanna610/Quadrature-amplitude-modulator/receiver/measurements/generator/from_gen_433MHz_40mV_2.png

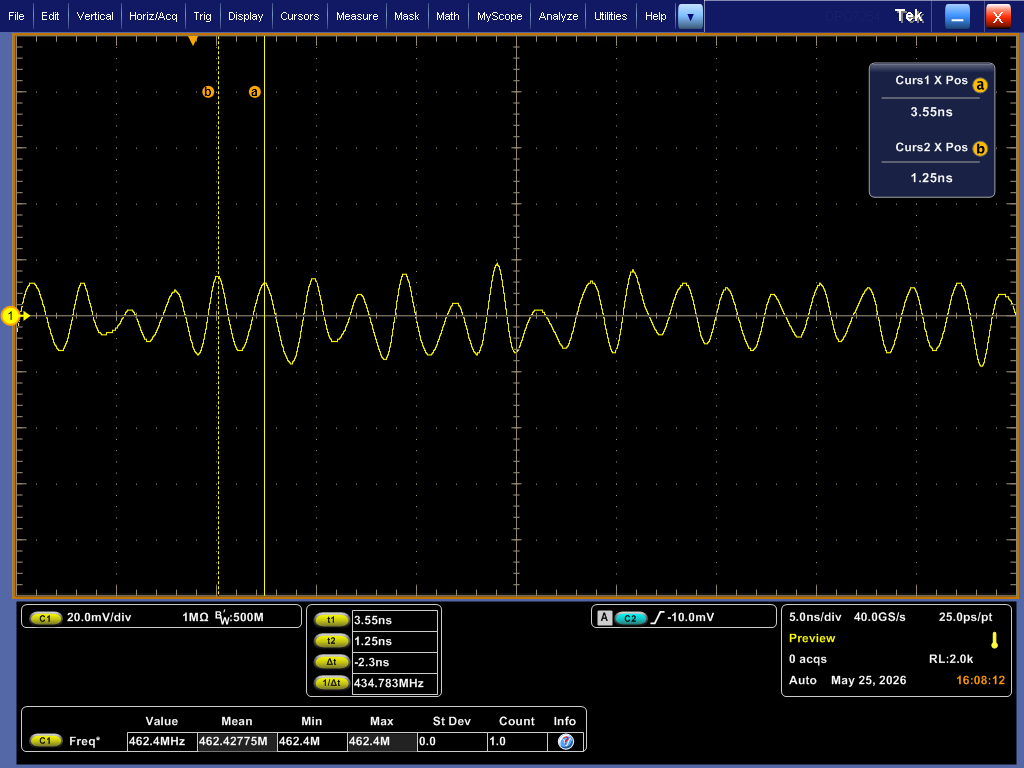
receiver/measurements/generator/from_gen_433MHz_40mV_2.png
