Joanna610/Quadrature-amplitude-modulator/receiver/measurements/generator/LNA_40mV_433MHz_gen_1.png

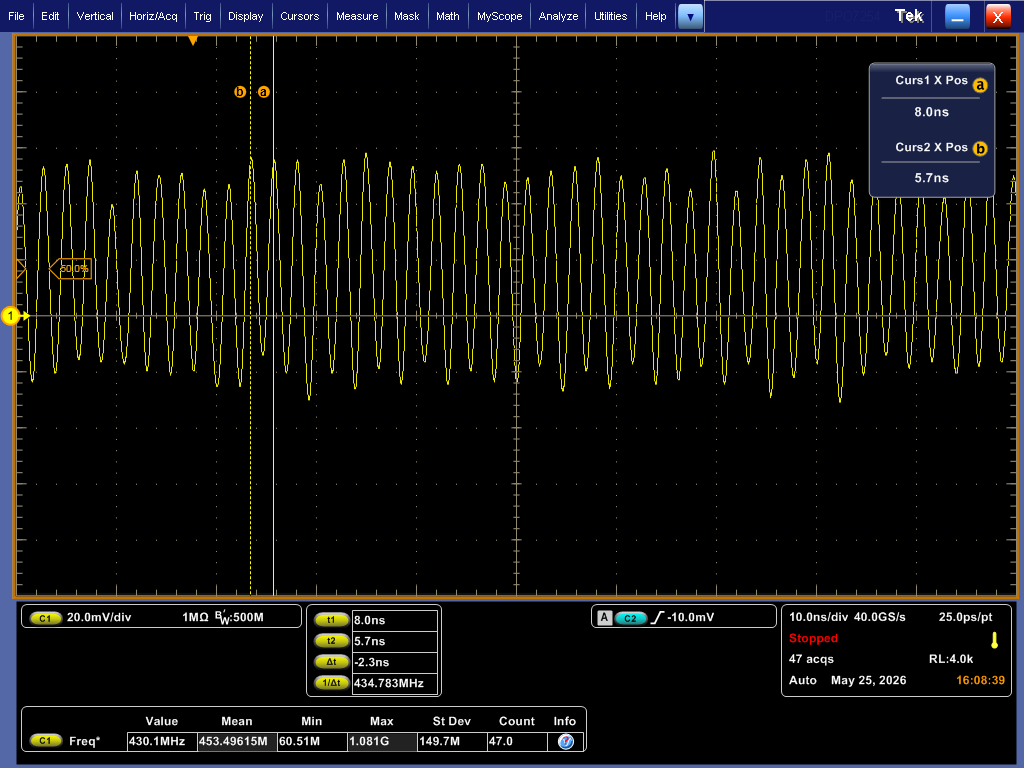
receiver/measurements/generator/LNA_40mV_433MHz_gen_1.png
