Joanna610/Quadrature-amplitude-modulator/receiver/measurements/Local_oscillator_receiver.png

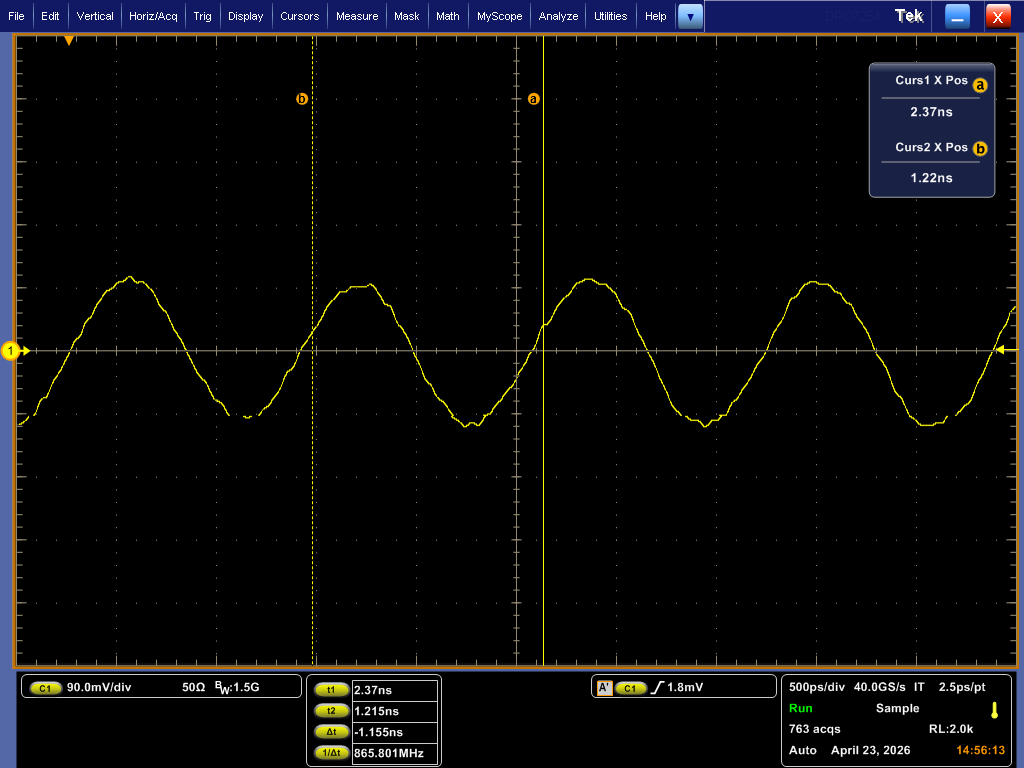
receiver/measurements/Local_oscillator_receiver.png
