Joanna610/Quadrature-amplitude-modulator/receiver/measurements/mod_dem_connected_with_cabel/mod_dem_output_I_3.png

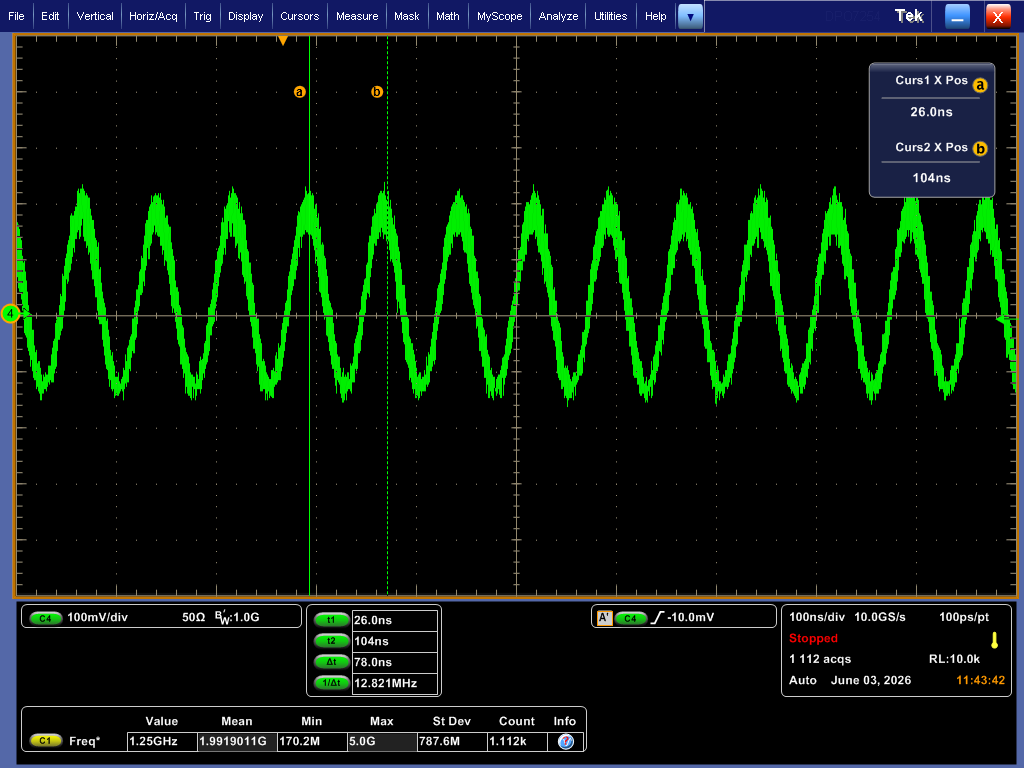
receiver/measurements/mod_dem_connected_with_cabel/mod_dem_output_I_3.png
