Joanna610/Quadrature-amplitude-modulator/receiver/measurements/mod_dem_connected_with_cabel/Mod_dem_phase_diff_1.png

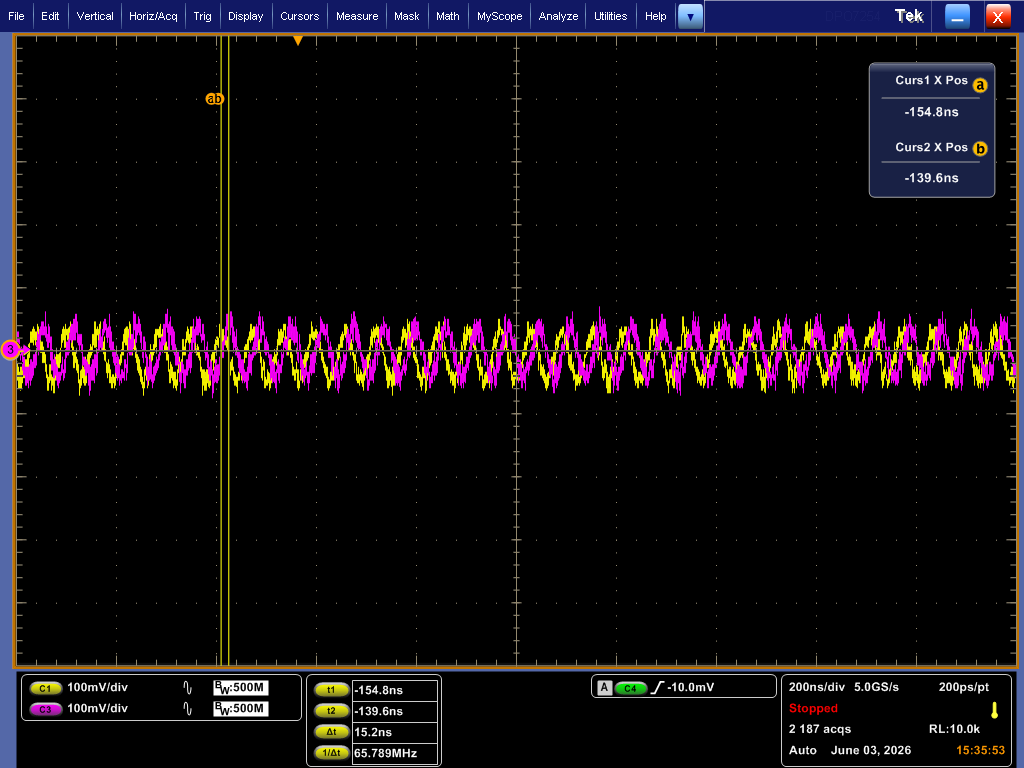
receiver/measurements/mod_dem_connected_with_cabel/Mod_dem_phase_diff_1.png
