Joanna610/Quadrature-amplitude-modulator/transmiter/measurements/DAC_2048.png

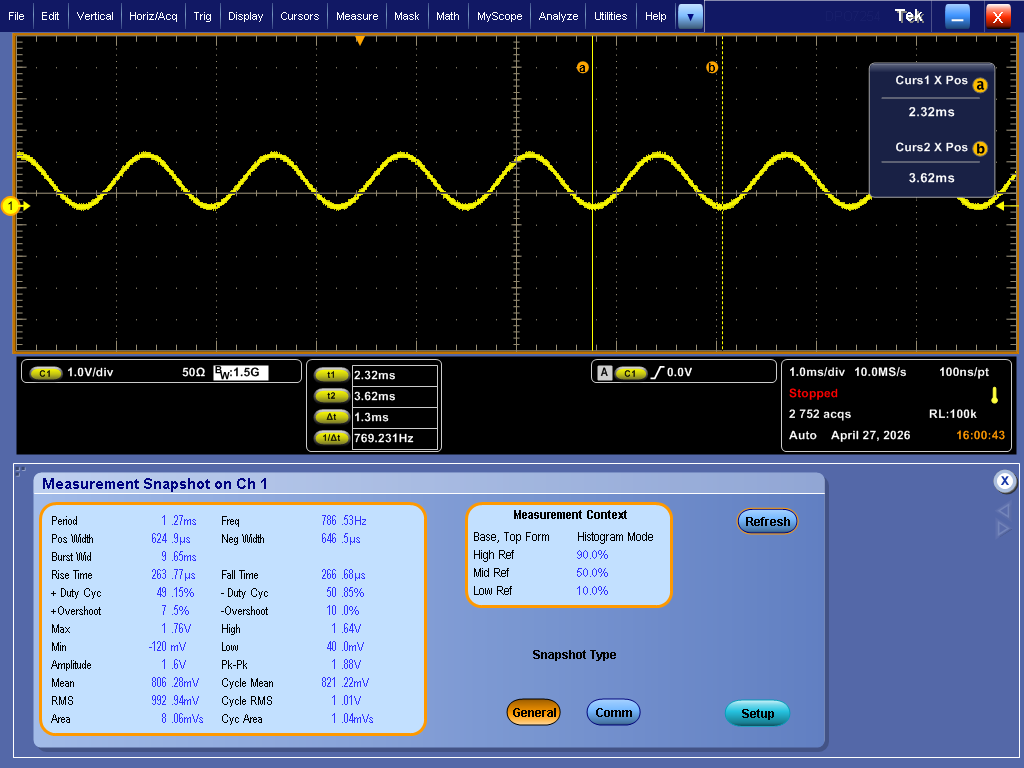
transmiter/measurements/DAC_2048.png
