Joanna610/Quadrature-amplitude-modulator/transmiter/measurements/DAC_2048_2.png

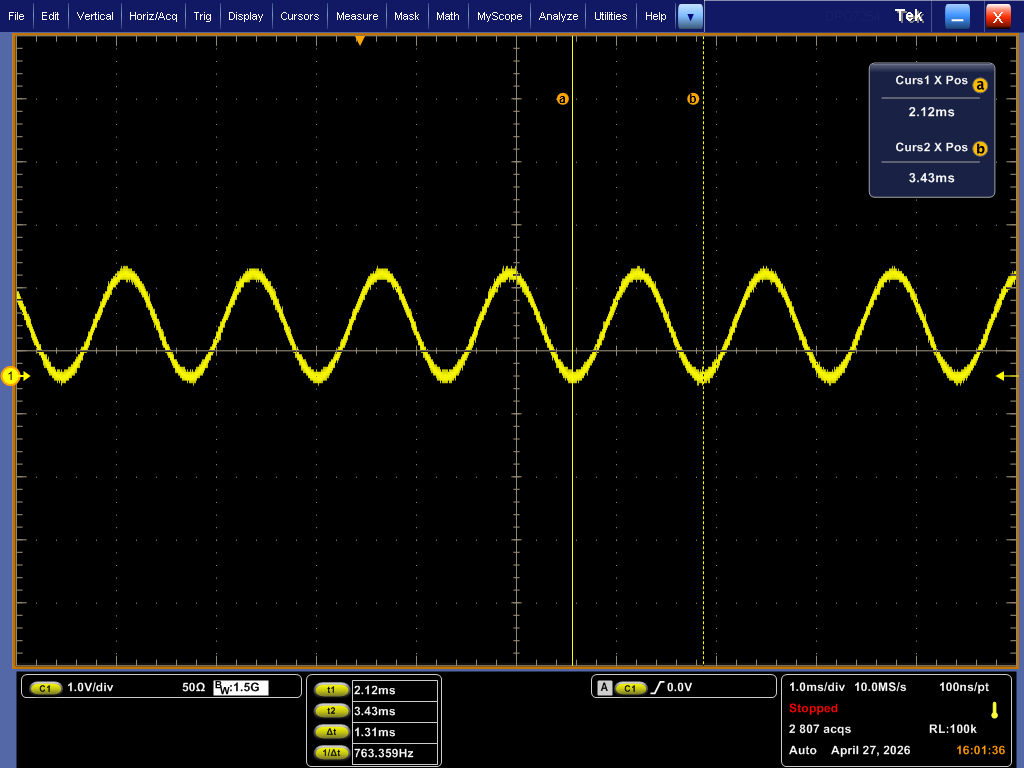
transmiter/measurements/DAC_2048_2.png
