Joanna610/Quadrature-amplitude-modulator/transmiter/measurements/DAC_4096.png

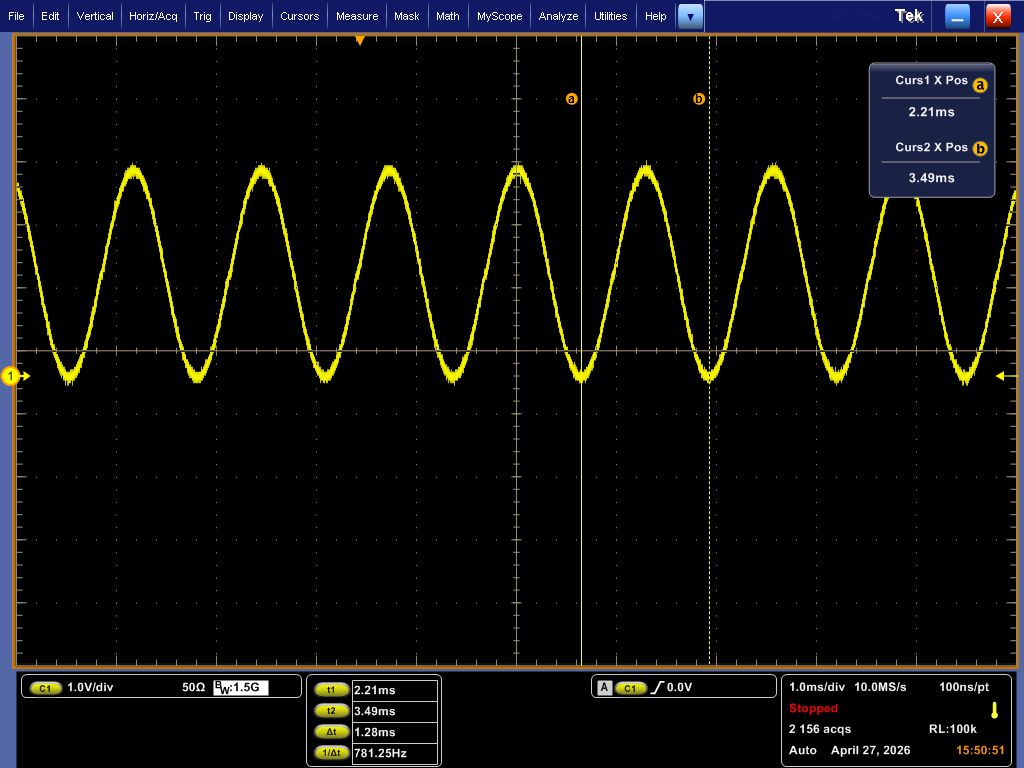
transmiter/measurements/DAC_4096.png
