Joanna610/Quadrature-amplitude-modulator/transmiter/measurements/DAC_4096_2.png

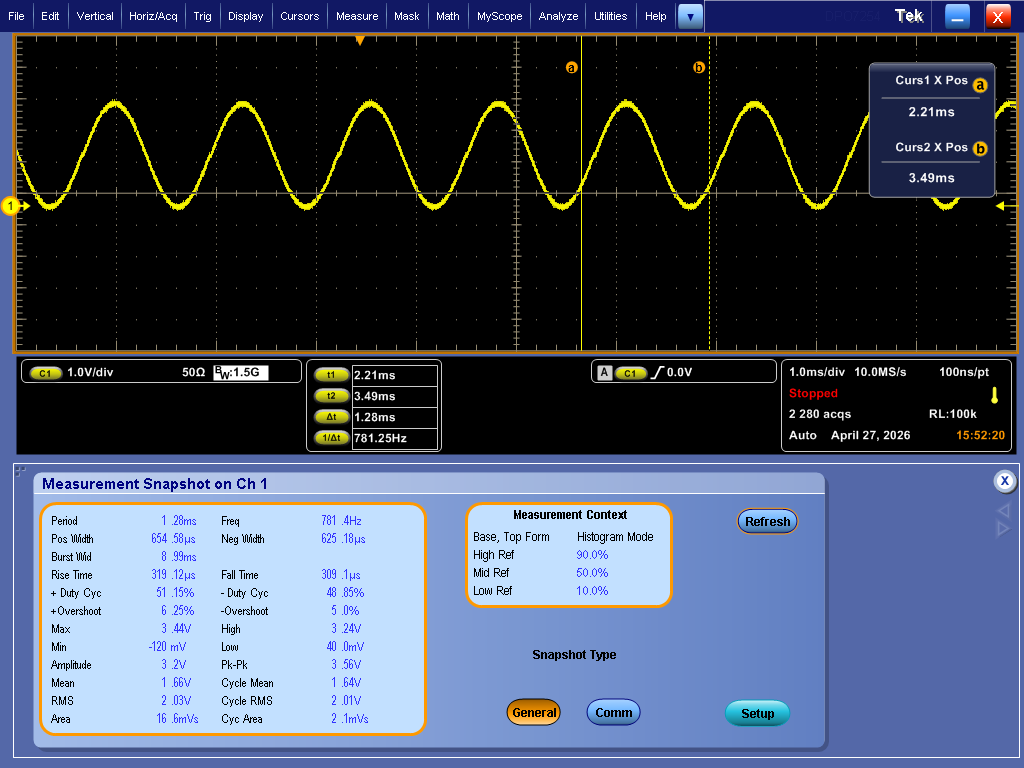
transmiter/measurements/DAC_4096_2.png
