Joanna610/Quadrature-amplitude-modulator/transmiter/measurements/first_VCO/negative_output.png

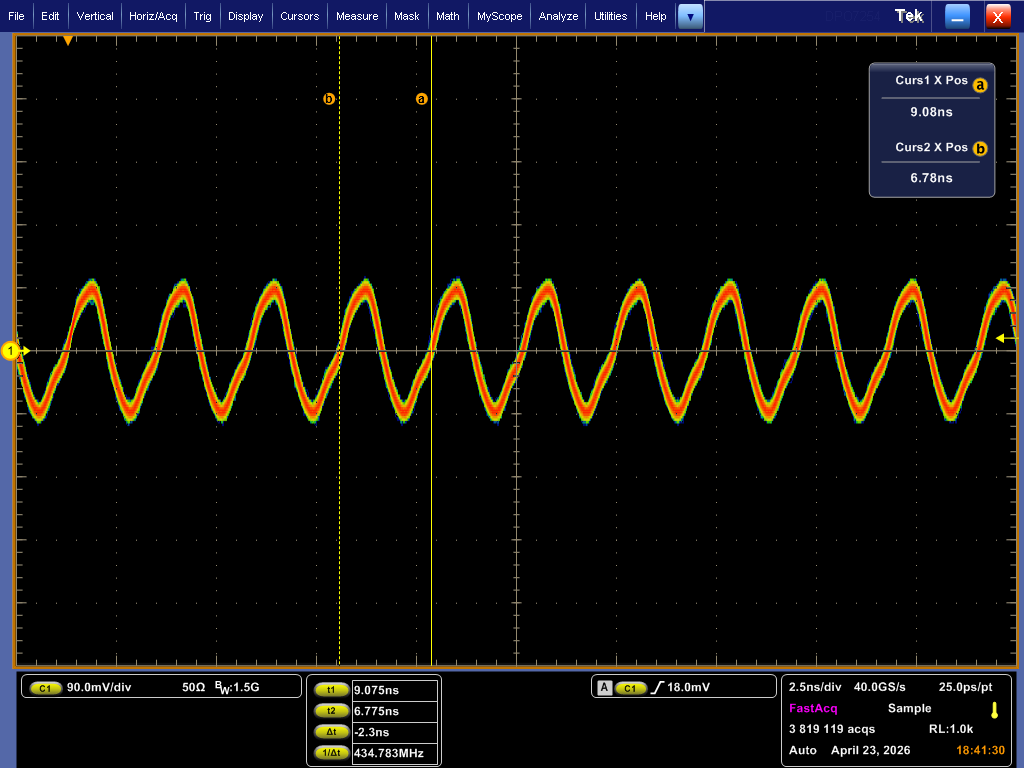
transmiter/measurements/first_VCO/negative_output.png
