Joanna610/Quadrature-amplitude-modulator/transmiter/measurements/first_VCO/positive_output_2.png

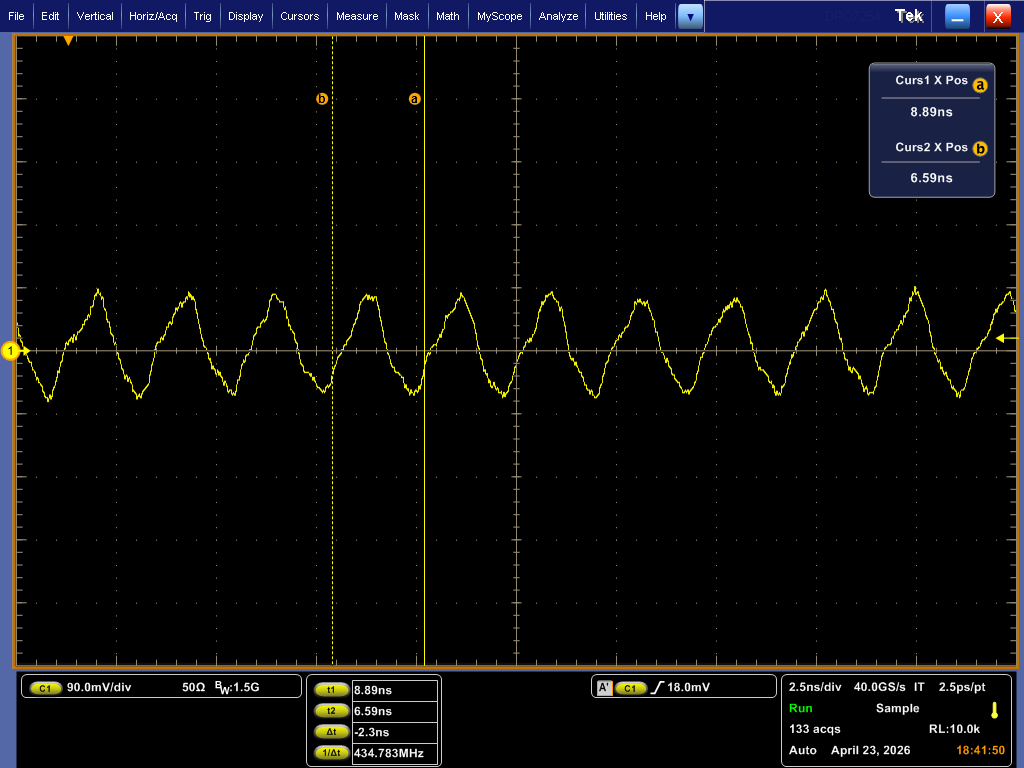
transmiter/measurements/first_VCO/positive_output_2.png
