Joanna610/Quadrature-amplitude-modulator/transmiter/measurements/neg.png

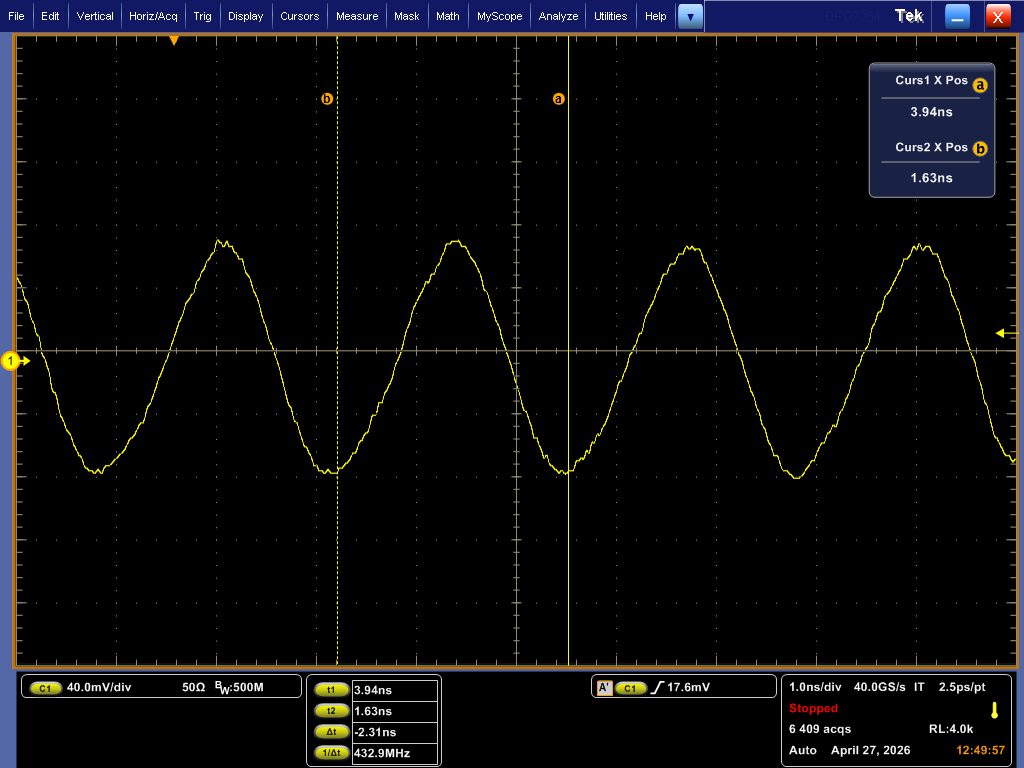
transmiter/measurements/neg.png
