Joanna610/Quadrature-amplitude-modulator/transmiter/measurements/negative.png

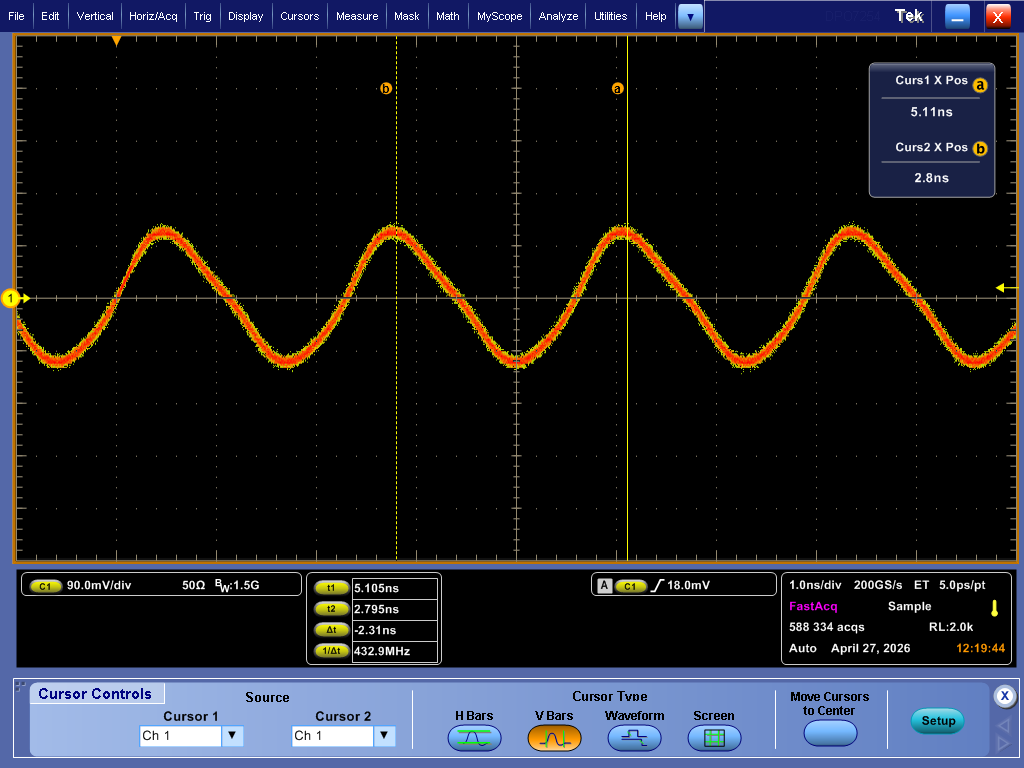
transmiter/measurements/negative.png
