Joanna610/Quadrature-amplitude-modulator/transmiter/measurements/new_measurement_21_05/1_mod3_amplified_DAC2_high_DAC1_high.png

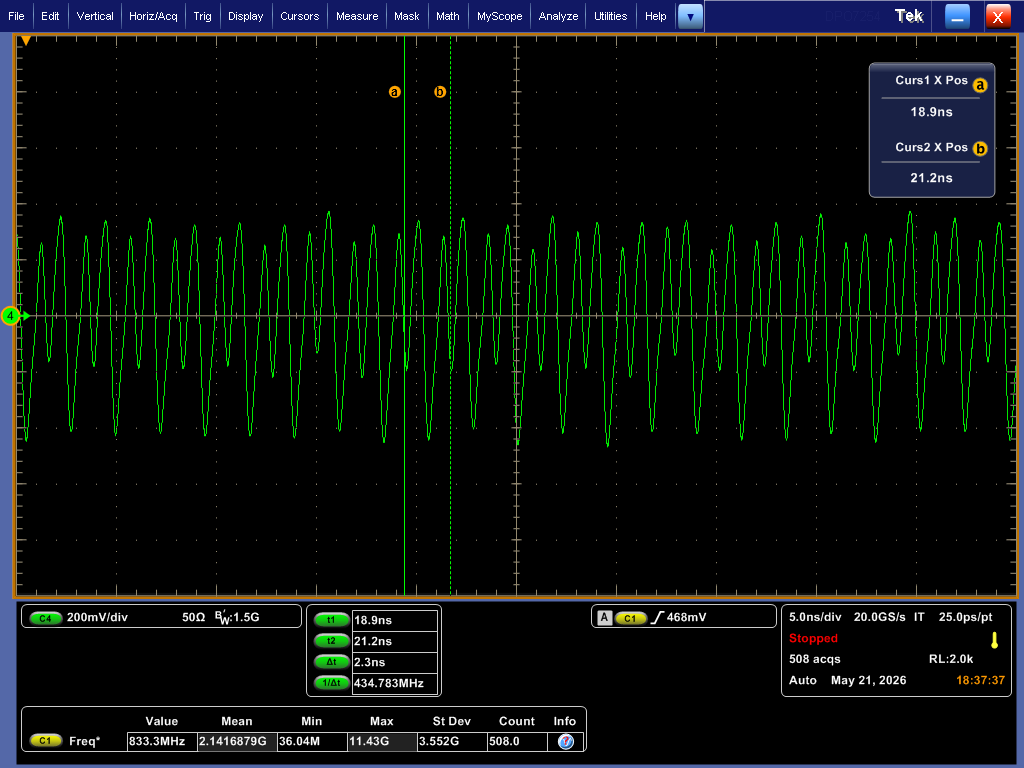
transmiter/measurements/new_measurement_21_05/1_mod3_amplified_DAC2_high_DAC1_high.png
