Joanna610/Quadrature-amplitude-modulator/transmiter/measurements/new_measurement_21_05/2_mod1_amplified_DAC2_low_DAC1_low.png

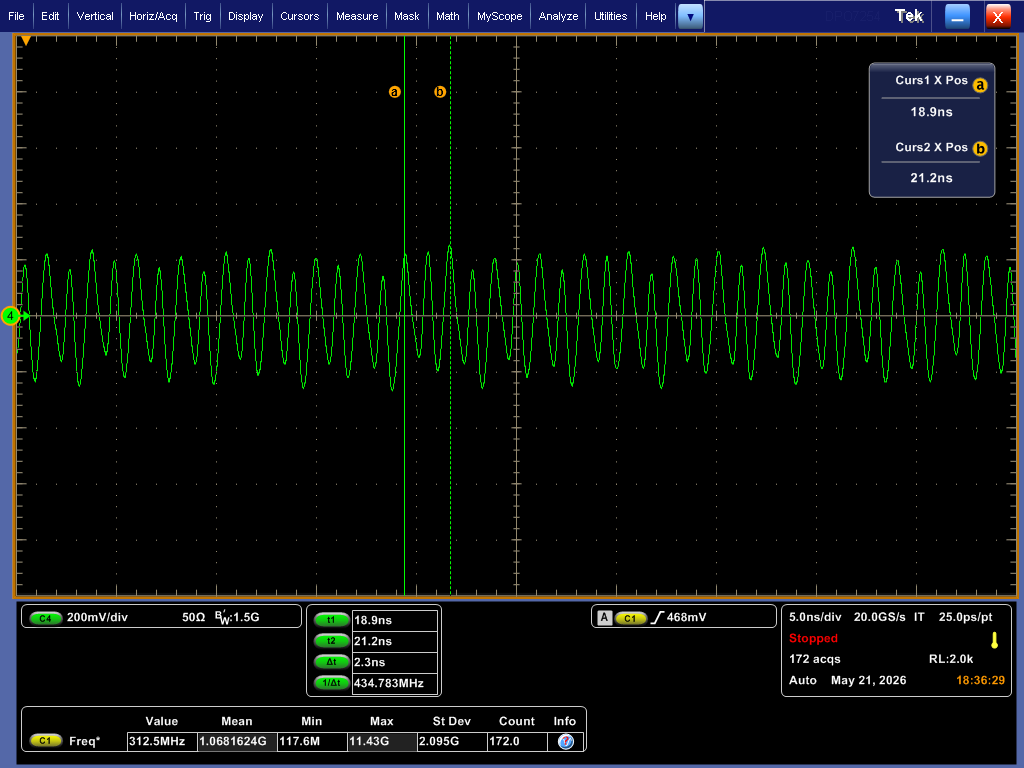
transmiter/measurements/new_measurement_21_05/2_mod1_amplified_DAC2_low_DAC1_low.png
