Joanna610/Quadrature-amplitude-modulator/transmiter/measurements/new_measurement_21_05/DAC_1.png

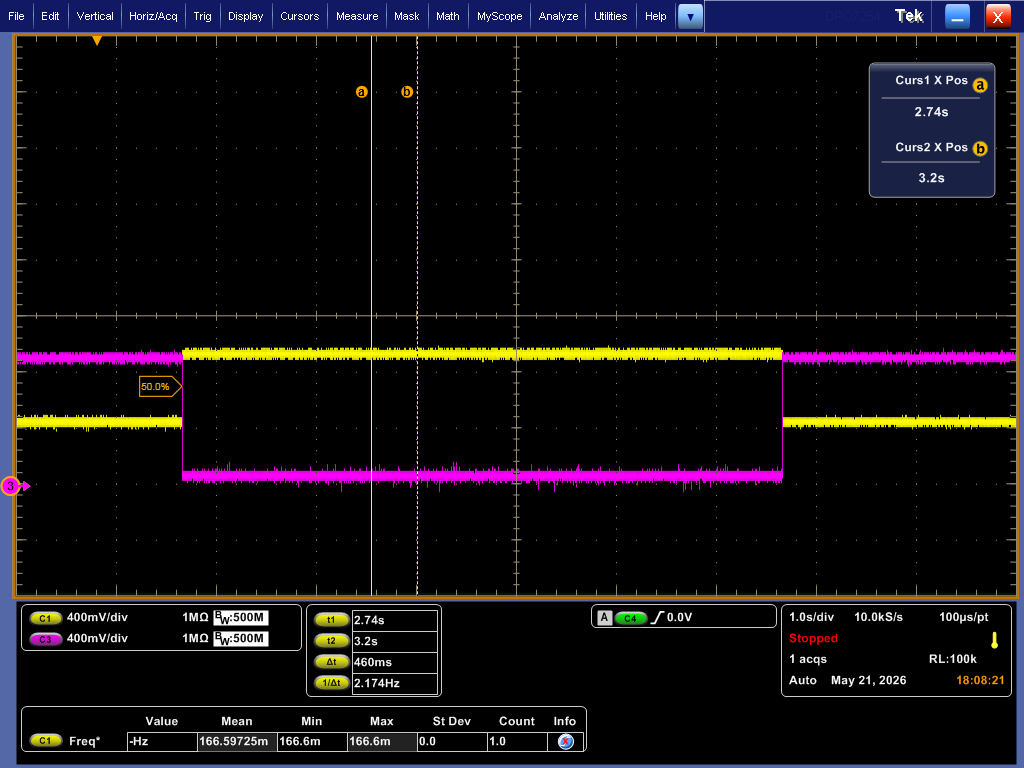
transmiter/measurements/new_measurement_21_05/DAC_1.png
