Joanna610/Quadrature-amplitude-modulator/transmiter/measurements/new_measurement_21_05/DACs_2.png

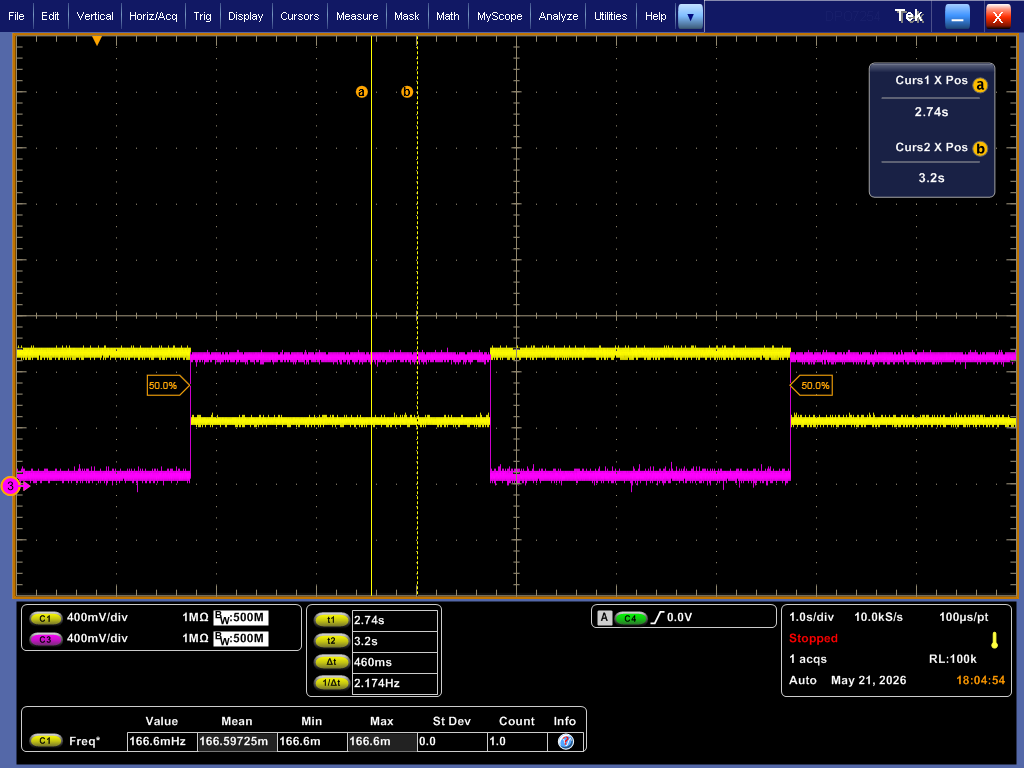
transmiter/measurements/new_measurement_21_05/DACs_2.png
