Joanna610/Quadrature-amplitude-modulator/transmiter/measurements/new_measurement_21_05/LO_positive.png

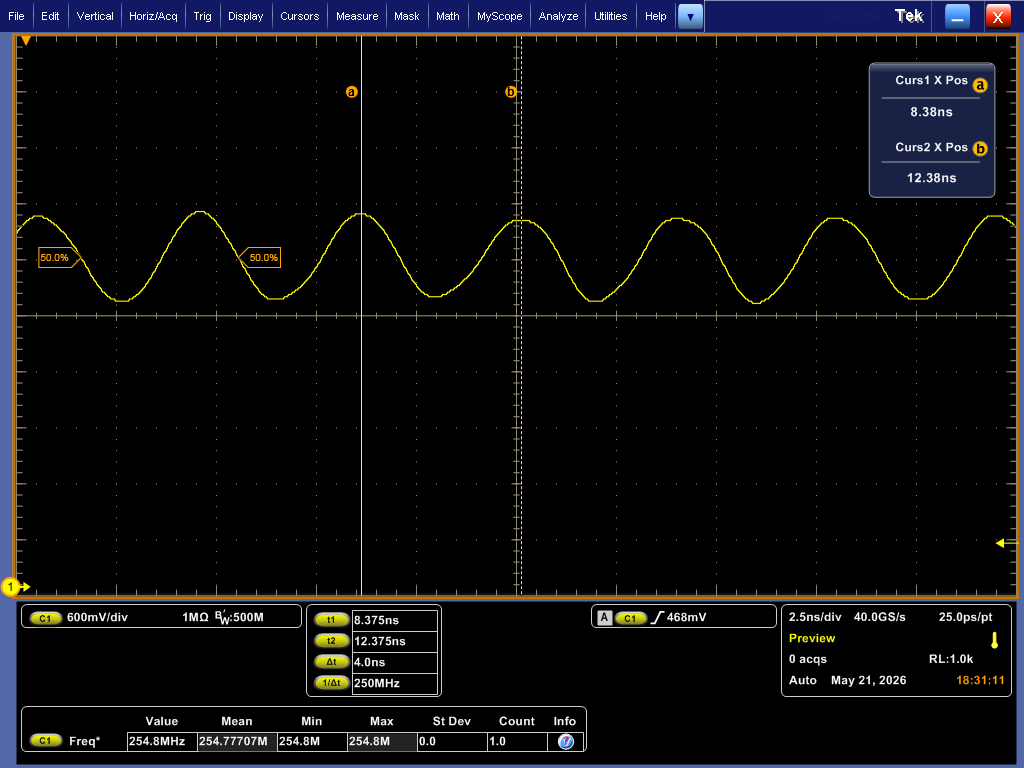
transmiter/measurements/new_measurement_21_05/LO_positive.png
