Joanna610/Quadrature-amplitude-modulator/transmiter/measurements/new_measurement_21_05/LO_receiver_newest.png

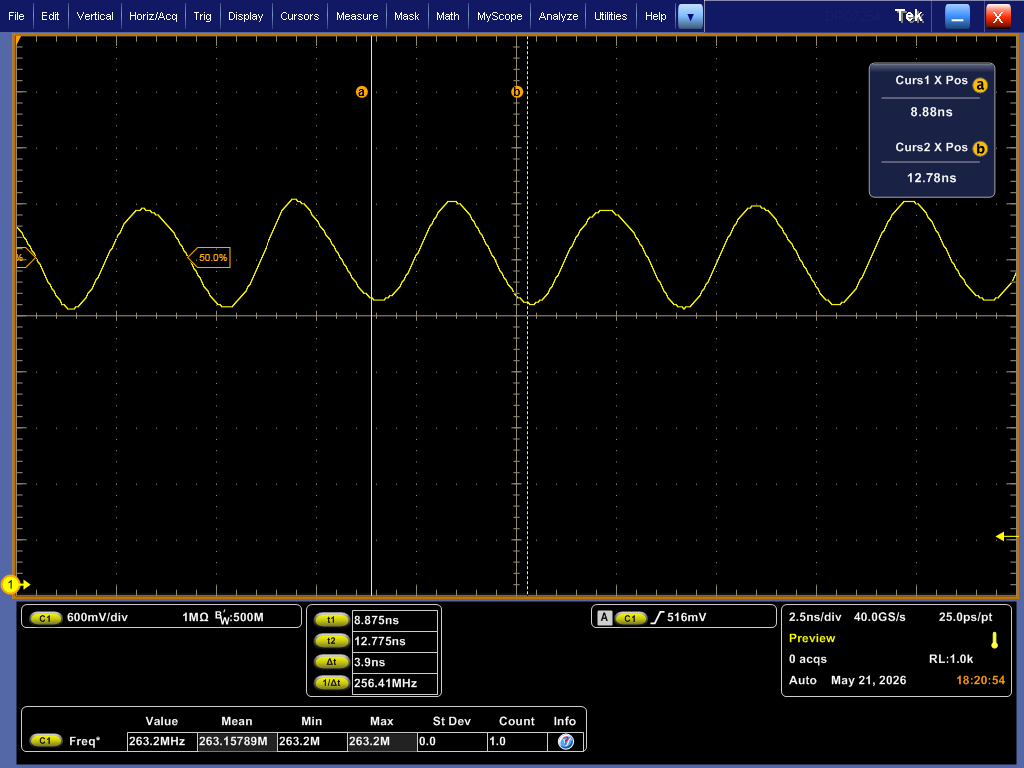
transmiter/measurements/new_measurement_21_05/LO_receiver_newest.png
