Joanna610/Quadrature-amplitude-modulator/transmiter/measurements/pos.png

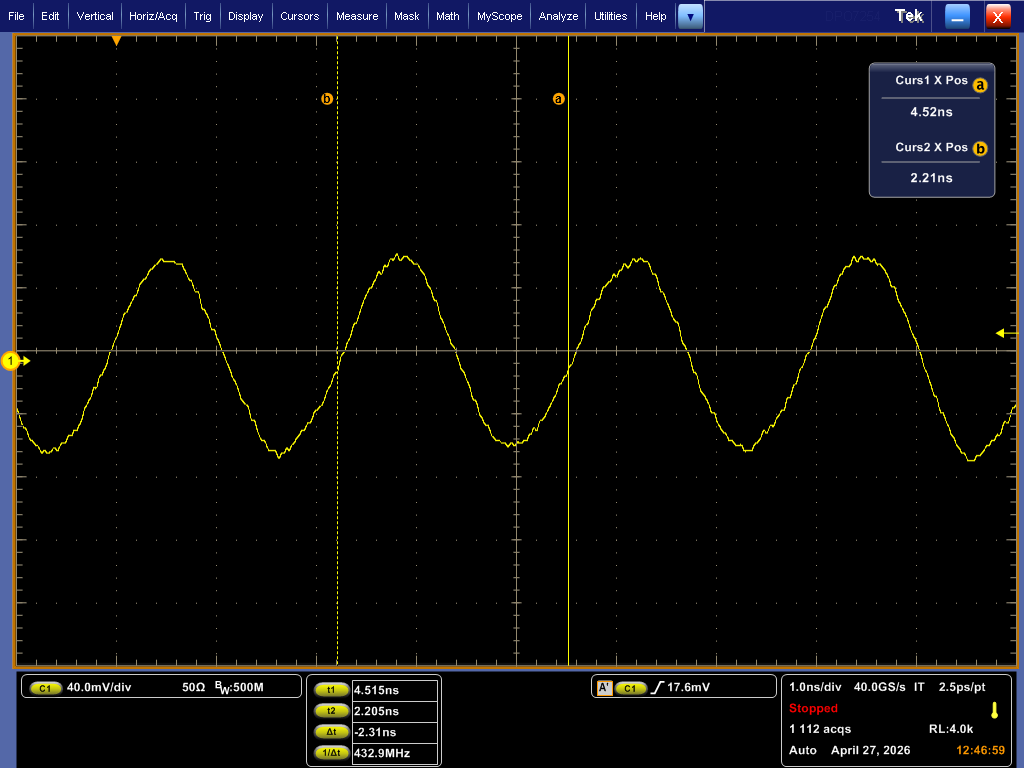
transmiter/measurements/pos.png
