Joanna610/Quadrature-amplitude-modulator/receiver/simulation/band_pass_filter.asc

C1: cap; 2p
C2: cap; 10p
C3: cap; 0.1p
C4: cap; 10p
C5: cap; 1n
L1: ind; 8.2n
L2: ind; 8.2n
R1: res; 50
R2: res; 50
V1: voltage; ""; AC 1 0
Named nets: output, 0
.ac dec 1000 100000k 1000000kHz
.tran 20m
Czebyshev, second order
