Joanna610/Quadrature-amplitude-modulator/receiver/simulation/Draft1.asc

R1: res; 1k
R2: res; 1k
U1: LTC6248
U2: LTC6248
V1: voltage; 5
V2: voltage; SINE(1.65 1.65 1k)
Named nets: 0, 3.3V
.tran 0.01
