Joanna610/Quadrature-amplitude-modulator/transmiter/simulation/differential_output_lt1638.asc

R1: res; 27k
R2: res; 27k
R3: res; 1k
R4: res; 1k
U3: opamp2; LMV796
U4: opamp2; LMV796
V1: voltage; 6
V2: voltage; SINE(1.66 1.66 1k); AC 1.65
V4: voltage; 3.3
Named nets: vcc, 0, out_of_phase, in_phase
.tran 0.003
LT1638
tutaj byc pewnym ze nie ma rezystora
.include LMV796.MOD
