Joanna610/Quadrature-amplitude-modulator/transmiter/simulation/differential_output_LT6237.asc

R1: res; 1k
R2: res; 1k
R3: res; 1k
R4: res; 1k
U1: LT6238
U3: LT6238
V1: voltage; 5
V2: voltage; SINE(1.65 1.65 1k); AC 1.65
V3: voltage; 5
V4: voltage; 3.3
Named nets: vcc, 0, out_of_phase, in_phase, -vcc
.tran 0.01
tutaj byc pewnym ze nie ma rezystora
LT6237
