Joanna610/Quadrature-amplitude-modulator/transmiter/simulation/Draft1.asc

Q1: npn
R1: res; 3.6k
R2: res; 47k
V1: voltage; PULSE(150m 850m 0 10n 10n 3 6)
V2: voltage; 850m
Named nets: 0
.tran 20
