Joanna610/Quadrature-amplitude-modulator/receiver/simulation/band_pass_filter_without_capacitor.asc

C1: cap; 0.5p
C2: cap; 13p
C4: cap; 13p
C5: cap; 0.5p
L1: ind; 10n
L2: ind; 10n
R1: res; 50
R2: res; 50
V1: voltage; ""; AC 1 0
Named nets: output, 0
.ac dec 1000 100000k 1000000kHz
.tran 20m
Czebyshev, second order
