Joanna610/Quadrature-amplitude-modulator/transmiter/simulation/Differential-LC-low-pass-filter.asc

C1: cap; 33p
C2: cap; 33p
L1: ind; 100µ
L2: ind; 100µ
R1: res; 50
R2: res; 50
R3: res; 100
V1: voltage; SINE(500m 500m 20k); AC 1 1
V2: voltage; SINE(500m 500m 20k); AC 1 1
Named nets: POSITIVE, NEGATIVE, INPUT_POS, INPUT_NEG, 0
.tran 0.1m
.ac dec 1000 1 10000k
Those resistors are only for impedance matching
