Joanna610/Quadrature-amplitude-modulator/receiver/simulation/band_pass_filter_Pawel.asc

C1: cap; 193.2f
C2: cap; 1.153p
C3: cap; 5.07f
C4: cap; 1.153p
C5: cap; 193.2f
L1: ind; 100n
L2: ind; 100n
R1: res; 50
R2: res; 50
V1: voltage; ""; AC 1 0
Named nets: output, 0
.ac dec 1000 100000k 1000000kHz
.tran 20m
