Joanna610/Quadrature-amplitude-modulator/receiver/simulation/Band_pass_filter_2.asc

C1: cap; 2280p
C2: cap; 0.0213p
C3: cap; 2280p
C4: cap; 0.0213p
L1: ind; 0.0001µ
L2: ind; 6.34µ
L3: ind; 0.0001µ
L4: ind; 6.34µ
R1: res; 50
R2: res; 50
V1: voltage; ""; AC 1 1
Named nets: 0, out, in
.tran 10m
.ac dec 1000 1 1000000k
